liveboxandy/ZX-Spectrum-48K-Issue-2/STP/TI_TMS4532.step

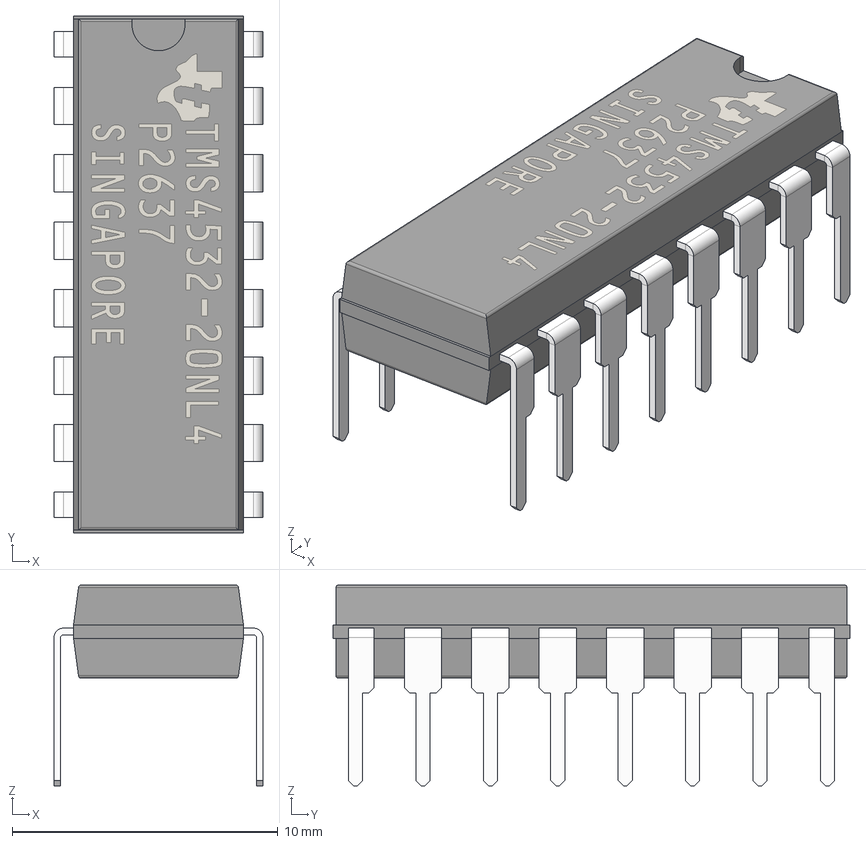
[picture p18: CAD file, 2026-09-27]
STP/TI_TMS4532.step
7.87 x 19.5 x 7.57 mm
Basic - DIP 7.62 v3
DIP Pin 14-20 v3
DIP Pin 14-20 v3(Mirror)
