liveboxandy/ZX-Spectrum-48K-Issue-2/STP/DO-41-5.10x2.60x15.24.STEP

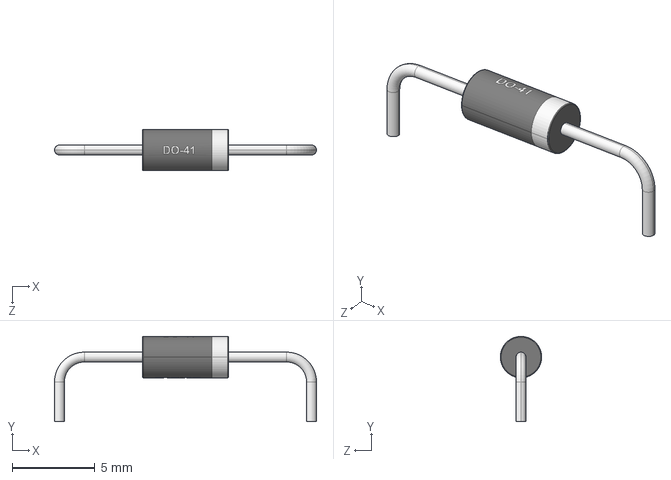
[picture p19: CAD file, 2026-09-27]
STP/DO-41-5.10x2.60x15.24.STEP
15.8 x 5.15 x 2.50 mm
