liveboxandy/ZX-Spectrum-48K-Issue-2/STP/Resistor-0414-11.5x4.5x20.32.STEP

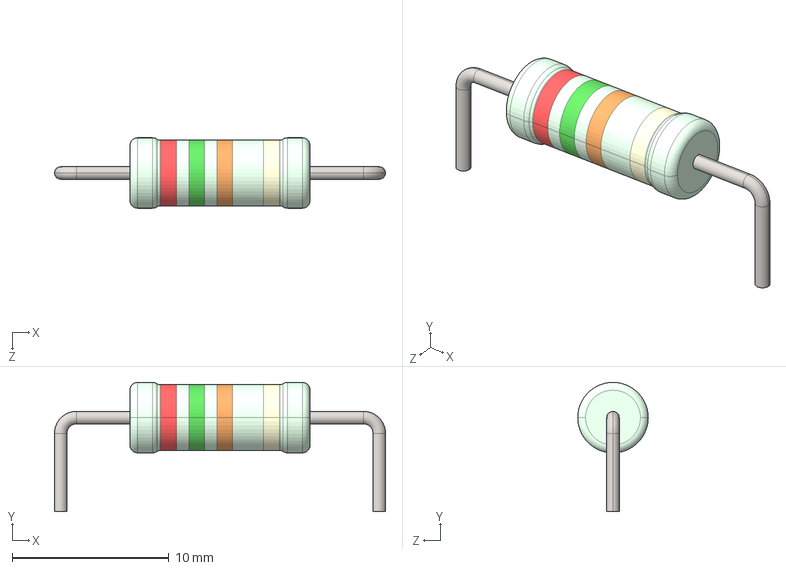
[picture p20: CAD file, 2026-09-27]
STP/Resistor-0414-11.5x4.5x20.32.STEP
21.1 x 8.25 x 4.50 mm
