liveboxandy/ZX-Spectrum-48K-Issue-2/STP/R_Axial_DIN0411_L9.9mm_D3.6mm_P12.70mm_Horizontal.step

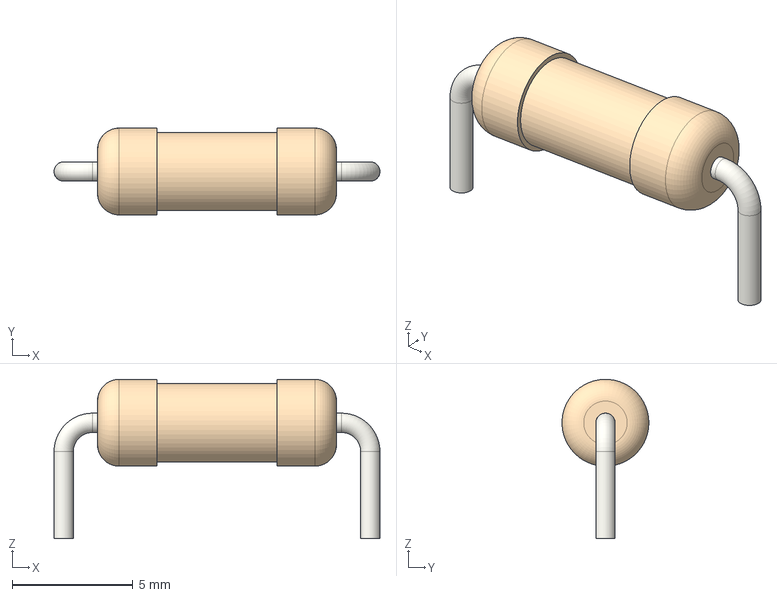
[picture p22: CAD file, 2026-09-27]
STP/R_Axial_DIN0411_L9.9mm_D3.6mm_P12.70mm_Horizontal.step
13.5 x 3.60 x 6.60 mm
