liveboxandy/ZX-Spectrum-48K-Issue-2/STP/DIP-18_W7.62mm.step

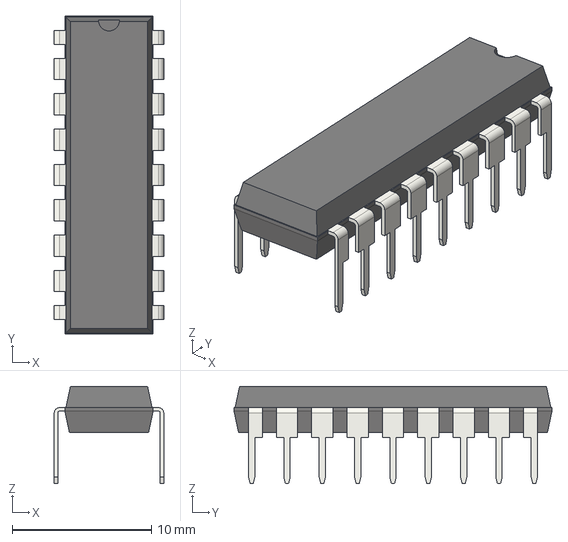
[picture p23: CAD file, 2026-09-27]
STP/DIP-18_W7.62mm.step
7.87 x 22.9 x 6.98 mm
