liveboxandy/ZX-Spectrum-48K-Issue-2/STP/Resistor-0414-11.5x4.5x15.24x3.STEP

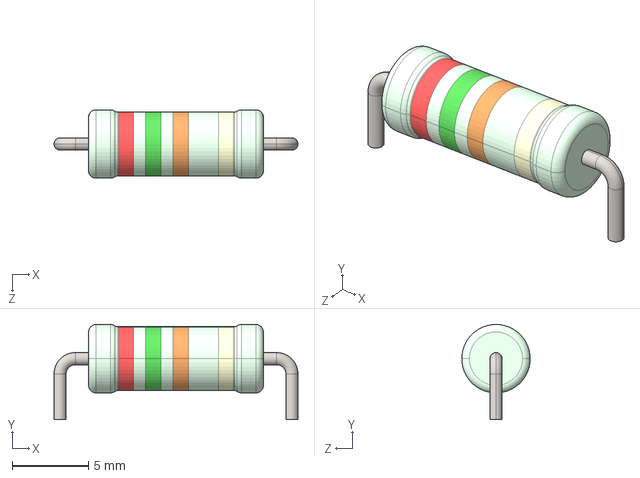
[picture p24: CAD file, 2026-09-27]
STP/Resistor-0414-11.5x4.5x15.24x3.STEP
16.0 x 6.25 x 4.50 mm
