liveboxandy/ZX-Spectrum-48K-Issue-2/STP/DO-41-5.10x2.60x10.16.STEP

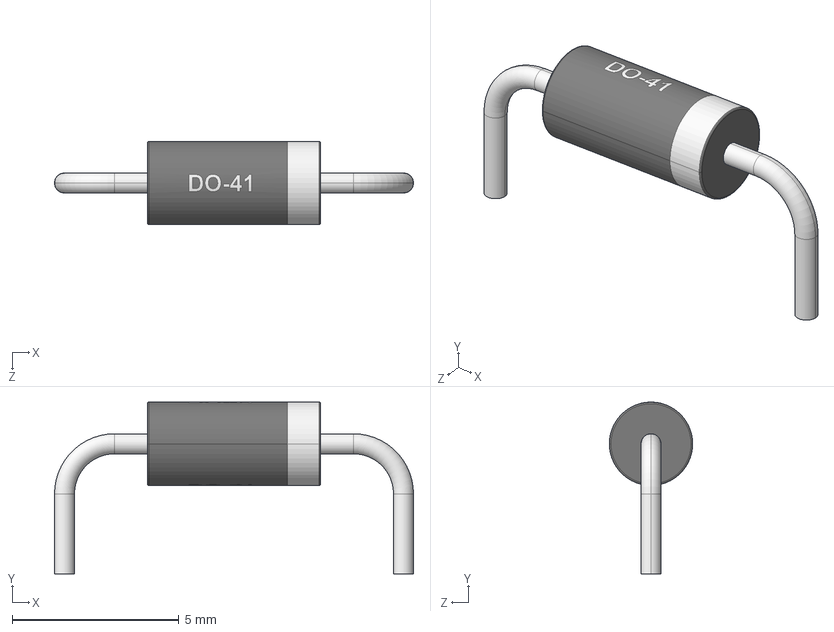
[picture p25: CAD file, 2026-09-27]
STP/DO-41-5.10x2.60x10.16.STEP
10.8 x 5.15 x 2.50 mm
