liveboxandy/ZX-Spectrum-48K-Issue-2/STP/Crystal-HC49-U.stp

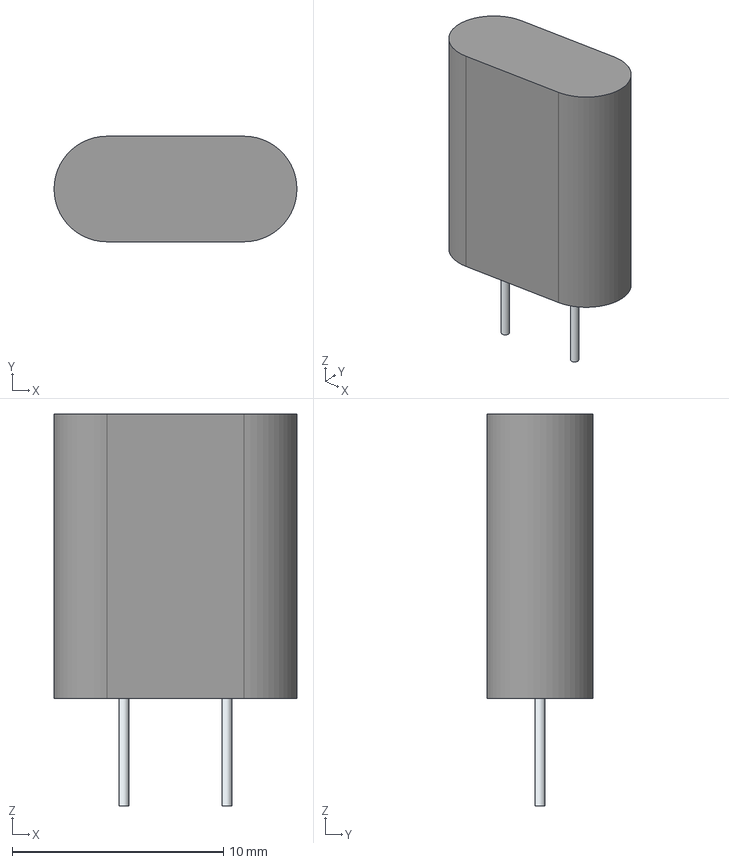
[picture p26: CAD file, 2026-09-27]
STP/Crystal-HC49-U.stp
11.5 x 5.00 x 18.6 mm
Leads
