liveboxandy/ZX-Spectrum-48K-Issue-2/STP/22-02-3053.stp

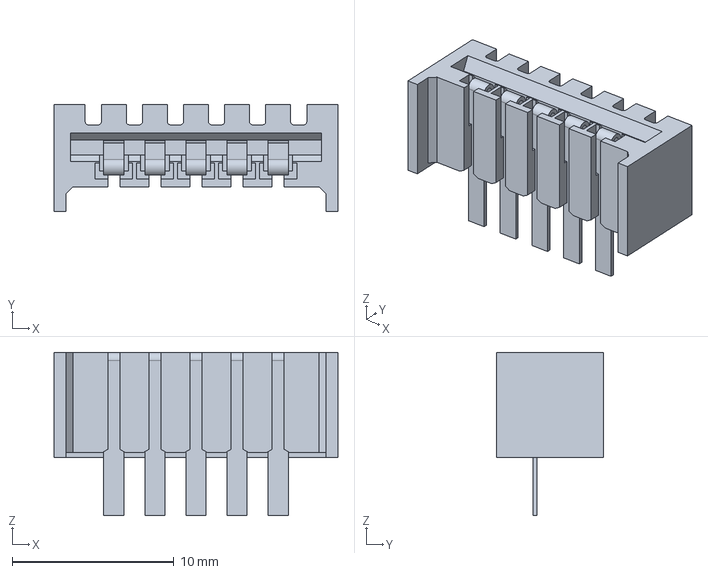
[picture p27: CAD file, 2026-09-27]
STP/22-02-3053.stp
17.6 x 6.60 x 10.1 mm
