liveboxandy/ZX-Spectrum-48K-Issue-2/STP/DIP-16_W7.62mm_Socket.step

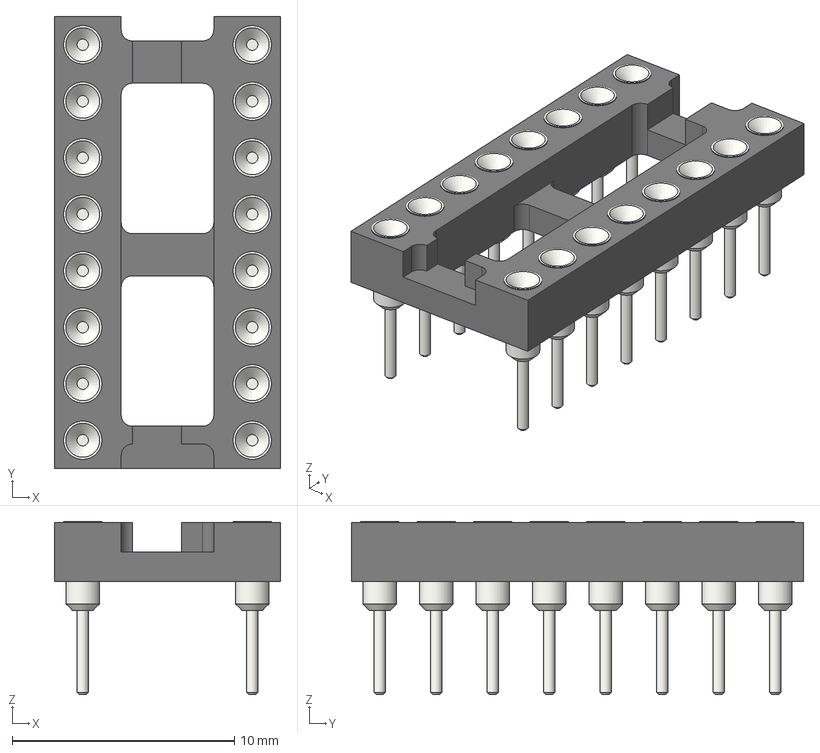
[picture p28: CAD file, 2026-09-27]
STP/DIP-16_W7.62mm_Socket.step
10.2 x 20.3 x 7.79 mm
