liveboxandy/ZX-Spectrum-48K-Issue-2/STP/DO-41-5.10x2.60x22.86.STEP

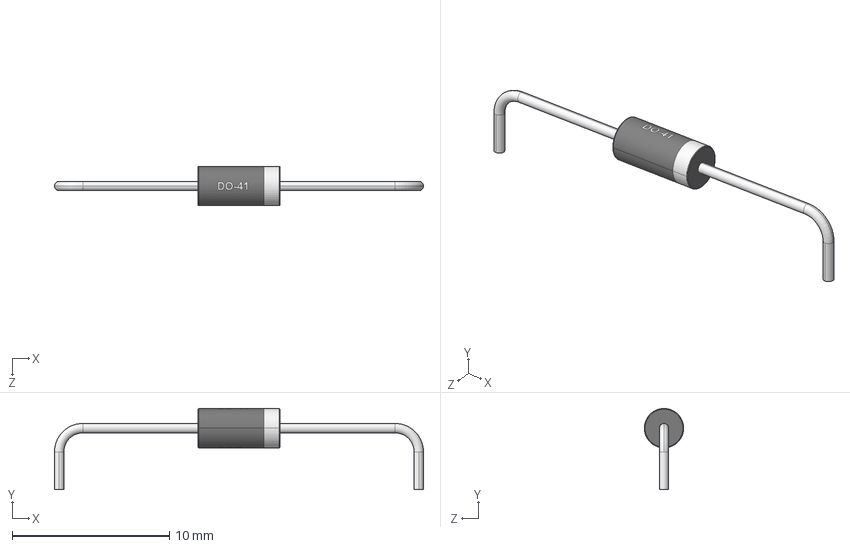
[picture p29: CAD file, 2026-09-27]
STP/DO-41-5.10x2.60x22.86.STEP
23.5 x 5.15 x 2.50 mm
