liveboxandy/ZX-Spectrum-48K-Issue-2/STP/DIP-14_W7.62mm_Socket.step

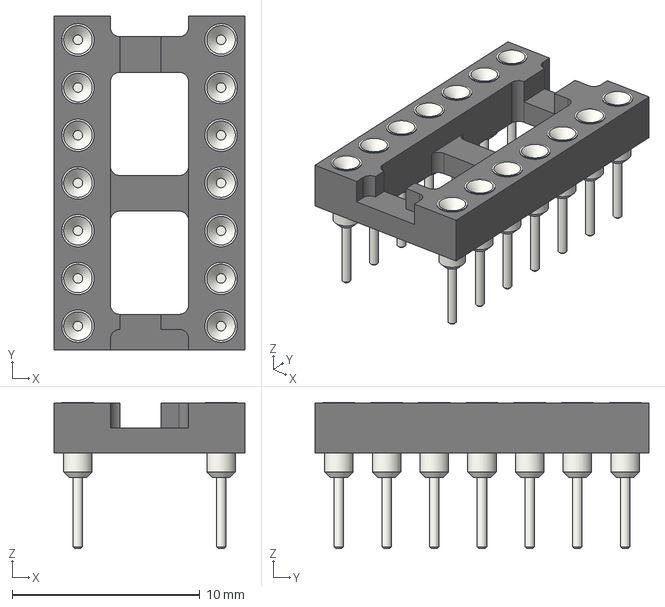
[picture p30: CAD file, 2026-09-27]
STP/DIP-14_W7.62mm_Socket.step
10.2 x 17.8 x 7.79 mm
