liveboxandy/ZX-Spectrum-48K-Issue-2/STP/Crystal-Low.stp

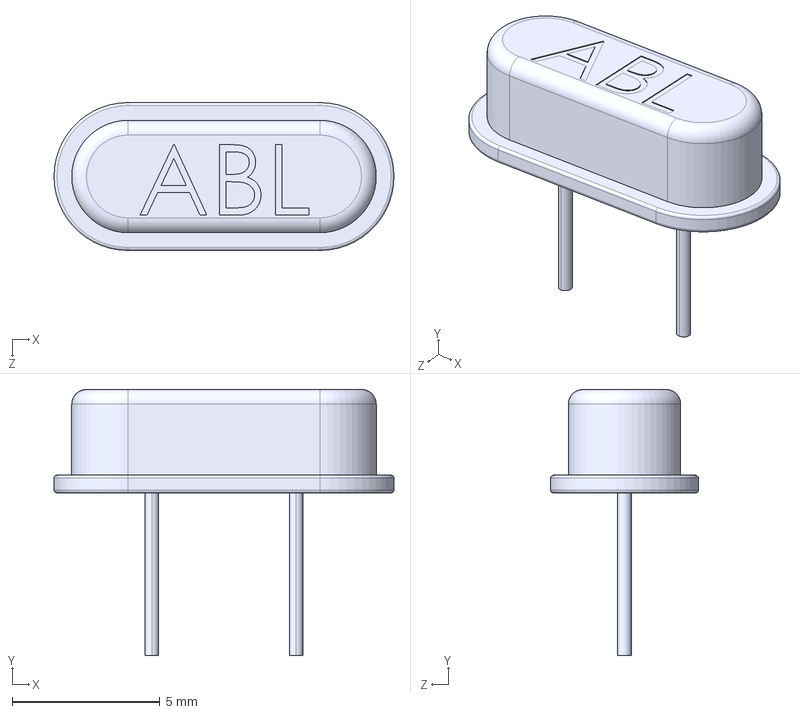
[picture p33: CAD file, 2026-09-27]
STP/Crystal-Low.stp
11.5 x 9.00 x 5.00 mm
