liveboxandy/ZX-Spectrum-48K-Issue-2/STP/Jumper.step

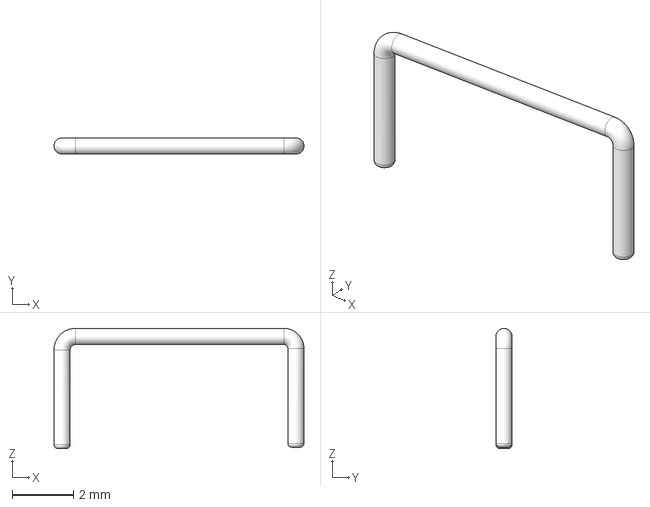
[picture p35: CAD file, 2026-09-27]
STP/Jumper.step
8.18 x 0.53 x 3.94 mm
