liveboxandy/ZX-Spectrum-48K-Issue-2/STP/LM7805CT_NOPB.stp

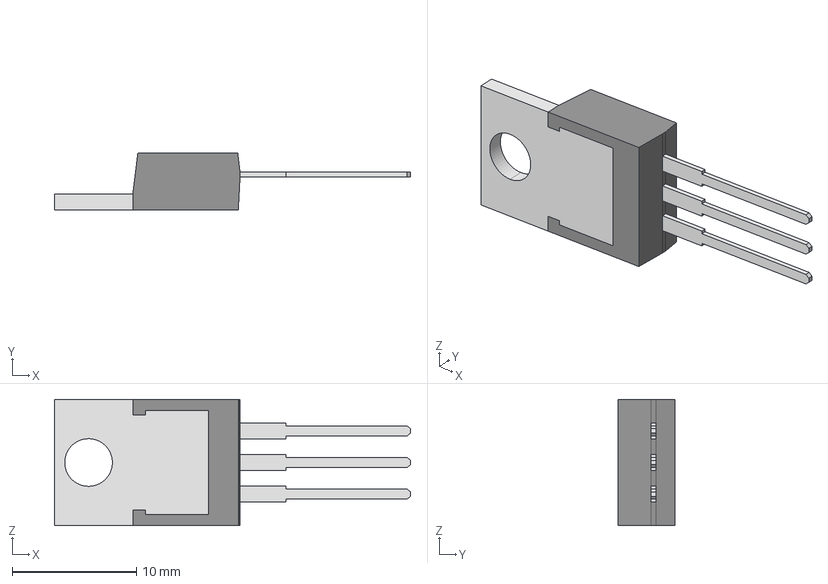
[picture p36: CAD file, 2026-09-27]
STP/LM7805CT_NOPB.stp
28.7 x 4.57 x 10.2 mm
T03B_BODY
T03B_LEAD x 3
T03B_HS
