liveboxandy/ZX-Spectrum-48K-Issue-2/STP/NS_LM1889N.step

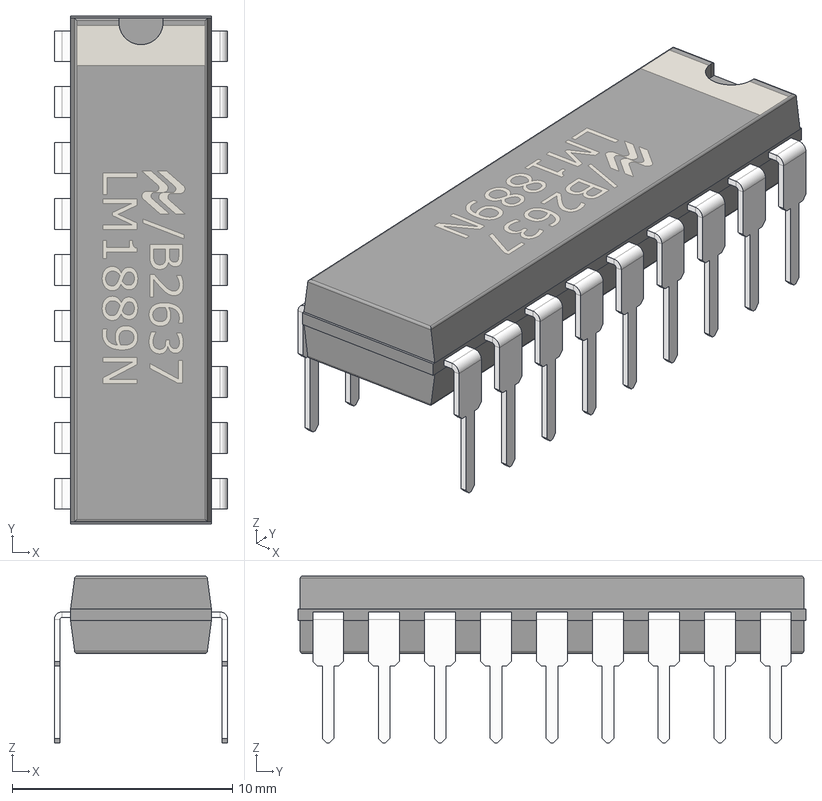
[picture p37: CAD file, 2026-09-27]
STP/NS_LM1889N.step
7.87 x 23.1 x 7.57 mm
Basic - DIP 7.62 v3
DIP Pin 14-20 v3
DIP Pin 14-20 v3(Mirror)
