liveboxandy/ZX-Spectrum-48K-Issue-2/STP/DO-35_P12.70_BA157.step

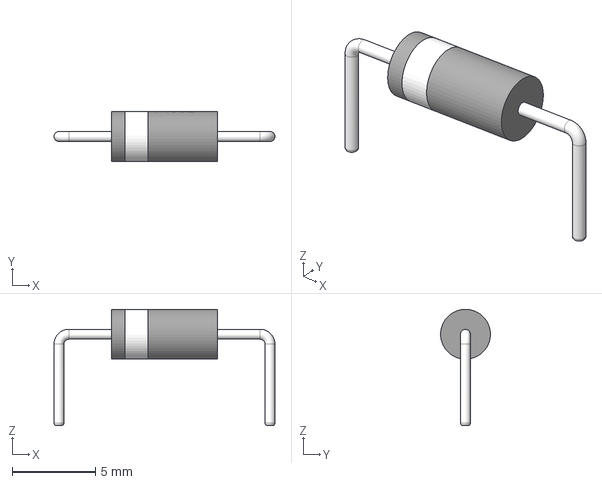
[picture p38: CAD file, 2026-09-27]
STP/DO-35_P12.70_BA157.step
13.3 x 3.00 x 7.00 mm
Wire
Diode Body
