liveboxandy/ZX-Spectrum-48K-Issue-2/STP/DIP-24_W10.16mm.step

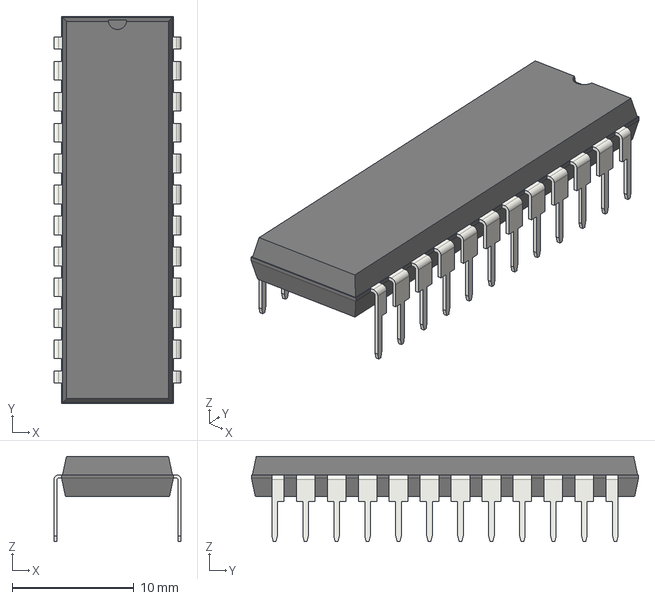
[picture p39: CAD file, 2026-09-27]
STP/DIP-24_W10.16mm.step
10.4 x 31.8 x 6.98 mm
