liveboxandy/ZX-Spectrum-48K-Issue-2/STP/LM7805 with Heatsink i3.step

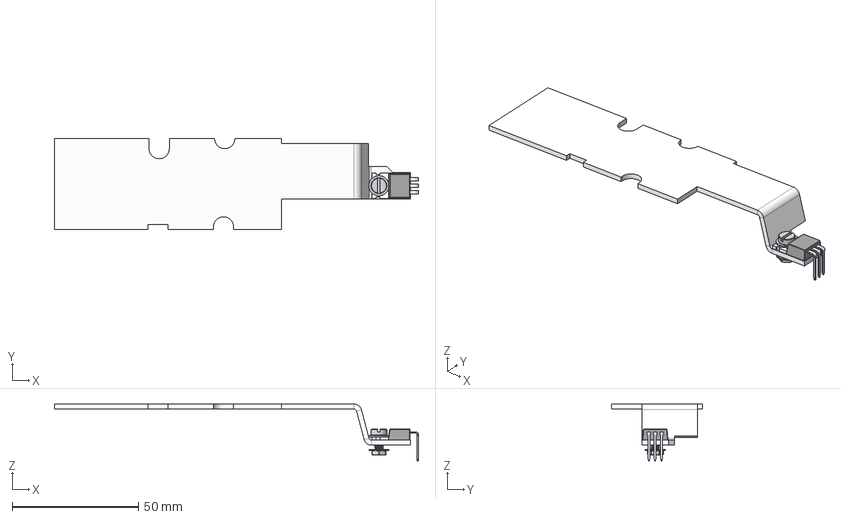
[picture p40: CAD file, 2026-09-27]
STP/LM7805 with Heatsink i3.step
144.3 x 36.0 x 22.5 mm
Heatsink
TO-220-3
Screw
93925A250_Internal Tooth Lock Washers
90695A033_Medium-Strength Steel Thin-Profile Hex Nut
Fibre Washer
