liveboxandy/ZX-Spectrum-48K-Issue-2/STP/CP 13x5x0.5x25.40.STEP

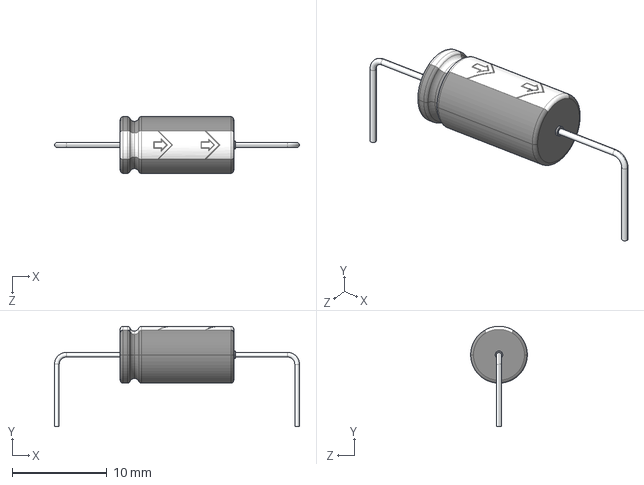
[picture p41: CAD file, 2026-09-27]
STP/CP 13x5x0.5x25.40.STEP
25.9 x 10.6 x 6.00 mm
