liveboxandy/ZX-Spectrum-48K-Issue-2/STP/Resistor-0207-6.3x2.4x15.24.STEP

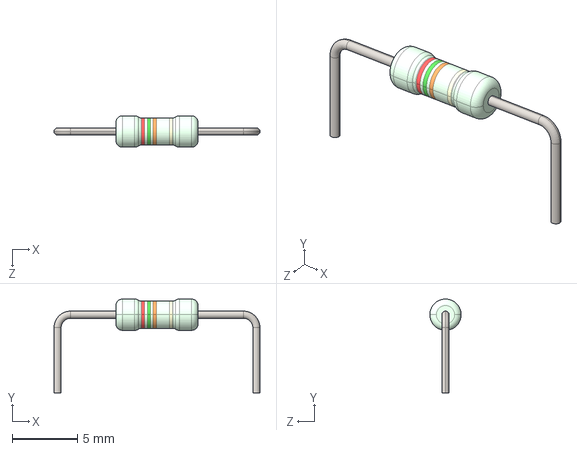
[picture p43: CAD file, 2026-09-27]
STP/Resistor-0207-6.3x2.4x15.24.STEP
15.8 x 7.20 x 2.40 mm
