liveboxandy/ZX-Spectrum-48K-Issue-2/STP/Capacitor Ceramic No Polarity axial 20.32.STEP

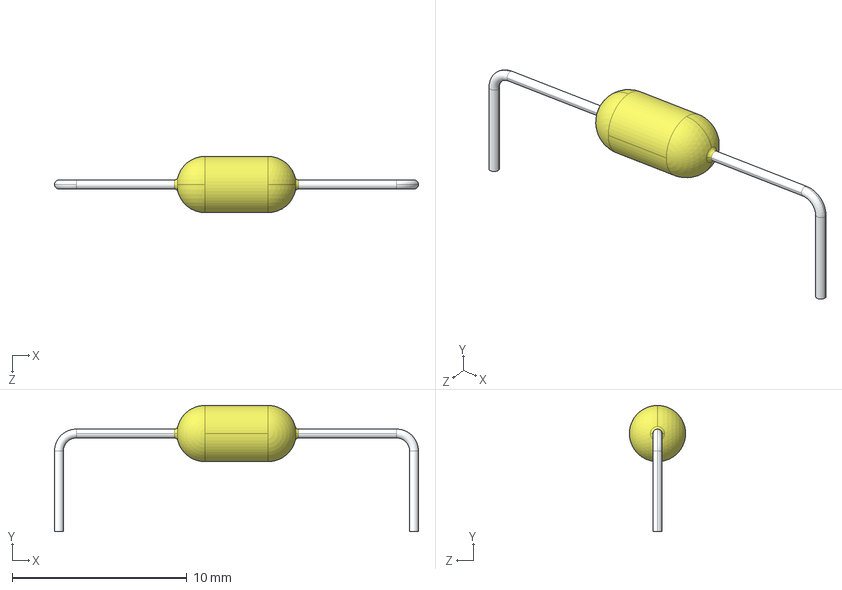
[picture p44: CAD file, 2026-09-27]
STP/Capacitor Ceramic No Polarity axial 20.32.STEP
20.8 x 7.22 x 3.22 mm
