liveboxandy/ZX-Spectrum-48K-Issue-2/STP/CP 13x5x0.5x17.78.STEP

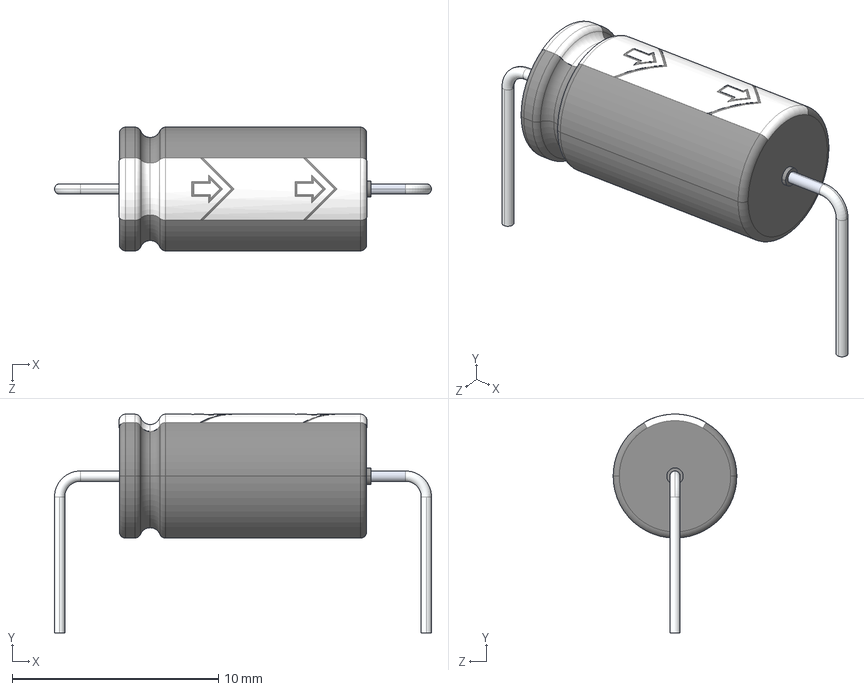
[picture p46: CAD file, 2026-09-27]
STP/CP 13x5x0.5x17.78.STEP
18.3 x 10.6 x 6.00 mm
