liveboxandy/ZX-Spectrum-48K-Issue-2/STP/DO-41-5.10x2.60x12.70.STEP

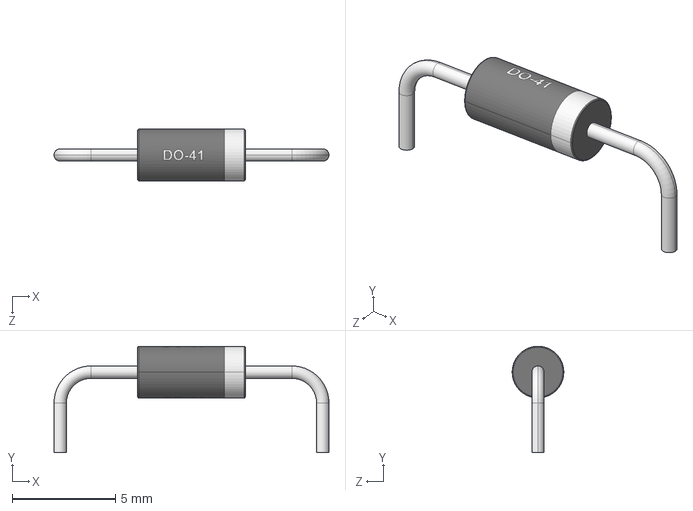
[picture p47: CAD file, 2026-09-27]
STP/DO-41-5.10x2.60x12.70.STEP
13.3 x 5.15 x 2.50 mm
