liveboxandy/ZX-Spectrum-48K-Issue-2/STP/22-02-3083.stp

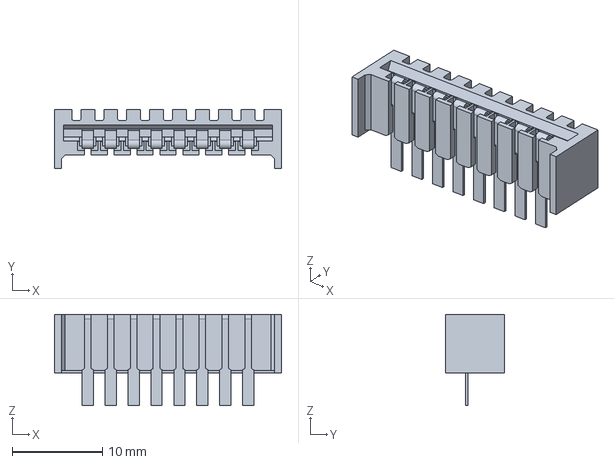
[picture p48: CAD file, 2026-09-27]
STP/22-02-3083.stp
25.2 x 6.60 x 10.1 mm
