liveboxandy/ZX-Spectrum-48K-Issue-2/STP/Pot 3339P-1-222LF.stp

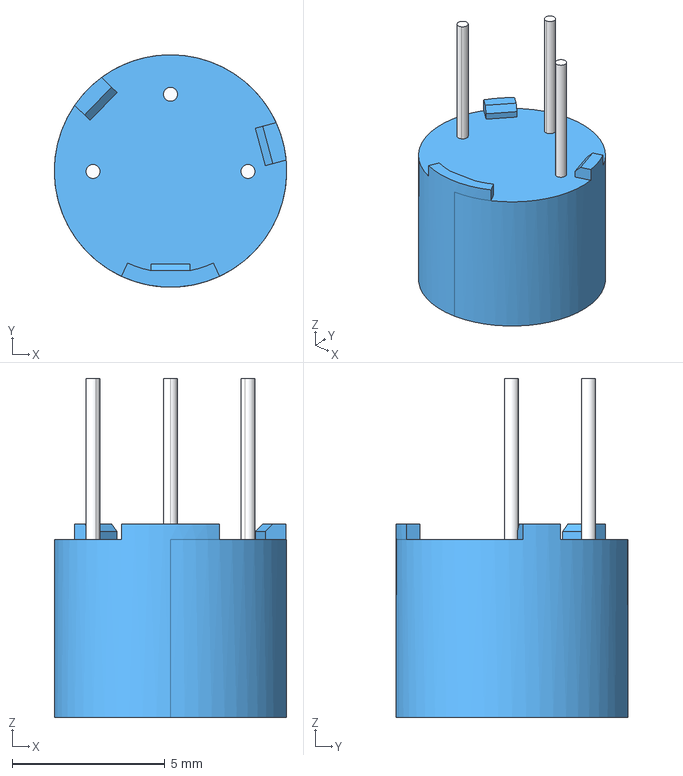
[picture p49: CAD file, 2026-09-27]
STP/Pot 3339P-1-222LF.stp
7.62 x 7.62 x 11.1 mm
