liveboxandy/ZX-Spectrum-48K-Issue-2/STP/ZTXxxx Kinked Triangle.STEP

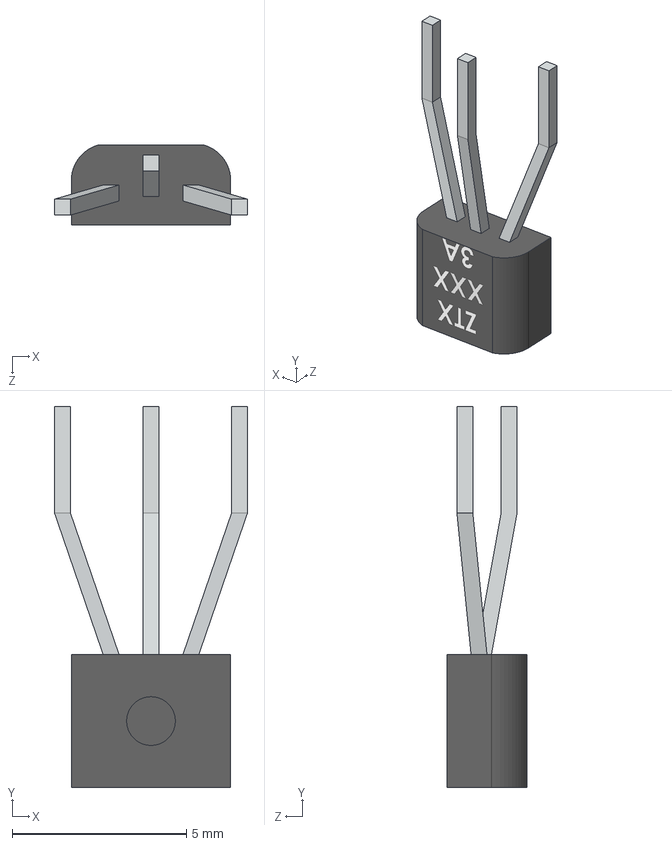
[picture p50: CAD file, 2026-09-27]
STP/ZTXxxx Kinked Triangle.STEP
5.54 x 10.9 x 2.29 mm
