liveboxandy/ZX-Spectrum-48K-Issue-2/STP/ZX Spectrum Speaker 40ohm.step

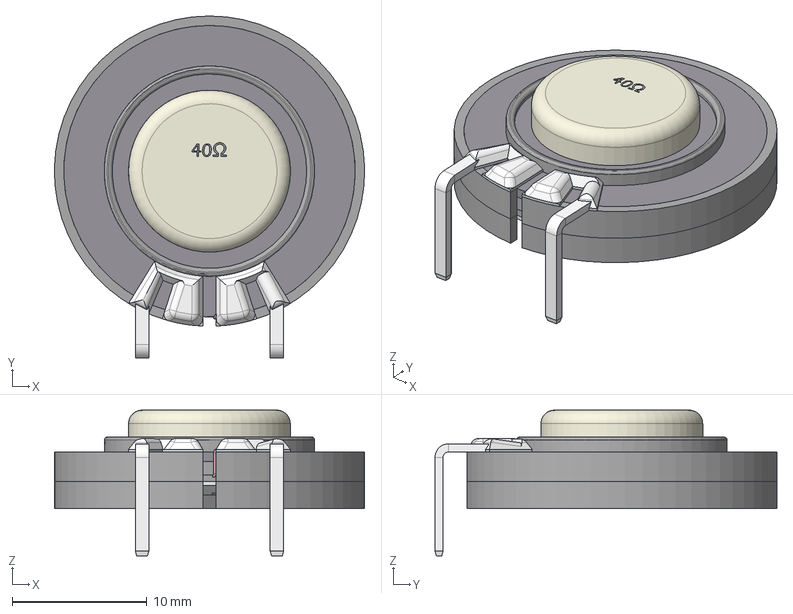
[picture p51: CAD file, 2026-09-27]
STP/ZX Spectrum Speaker 40ohm.step
23.0 x 25.4 x 10.8 mm
Magnet
Plastic Cover
Board
CopperWire
Pins
