liveboxandy/ZX-Spectrum-48K-Issue-2/STP/Resistor-0207-6.3x2.4x12.70.STEP

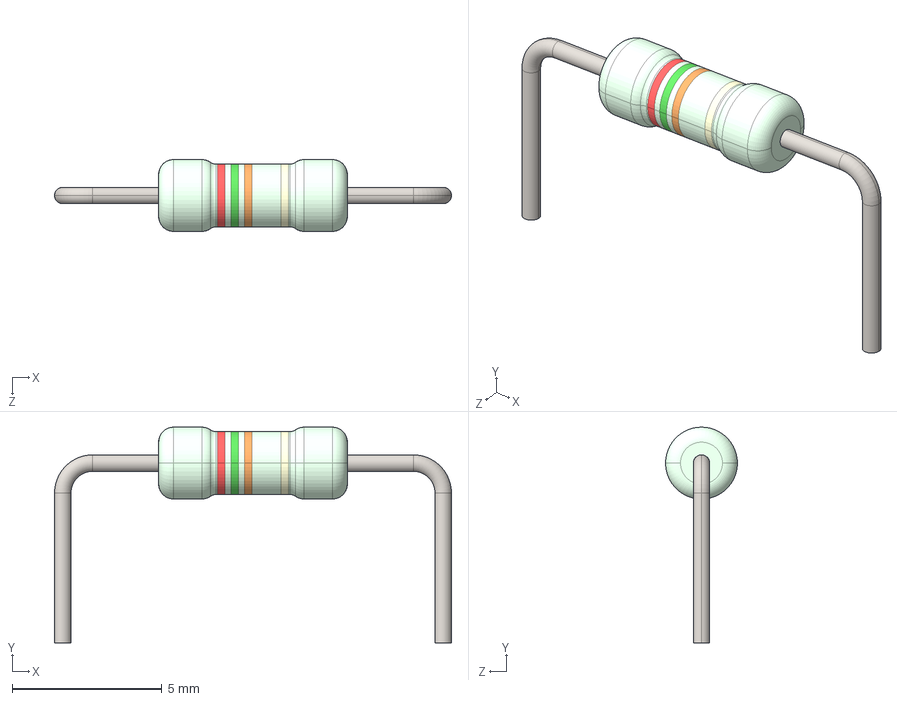
[picture p52: CAD file, 2026-09-27]
STP/Resistor-0207-6.3x2.4x12.70.STEP
13.3 x 7.20 x 2.40 mm
