liveboxandy/ZX-Spectrum-48K-Issue-2/STP/Resistor-0414-11.5x4.5x17.78.STEP

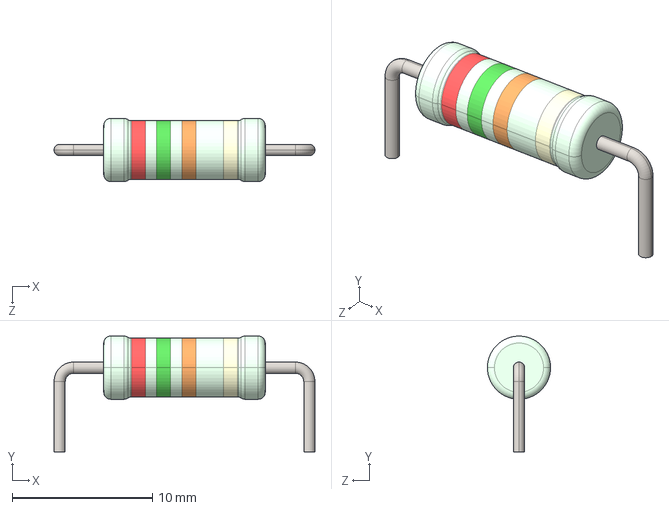
[picture p53: CAD file, 2026-09-27]
STP/Resistor-0414-11.5x4.5x17.78.STEP
18.6 x 8.25 x 4.50 mm
