liveboxandy/ZX-Spectrum-48K-Issue-2/STP/Speaker.stp

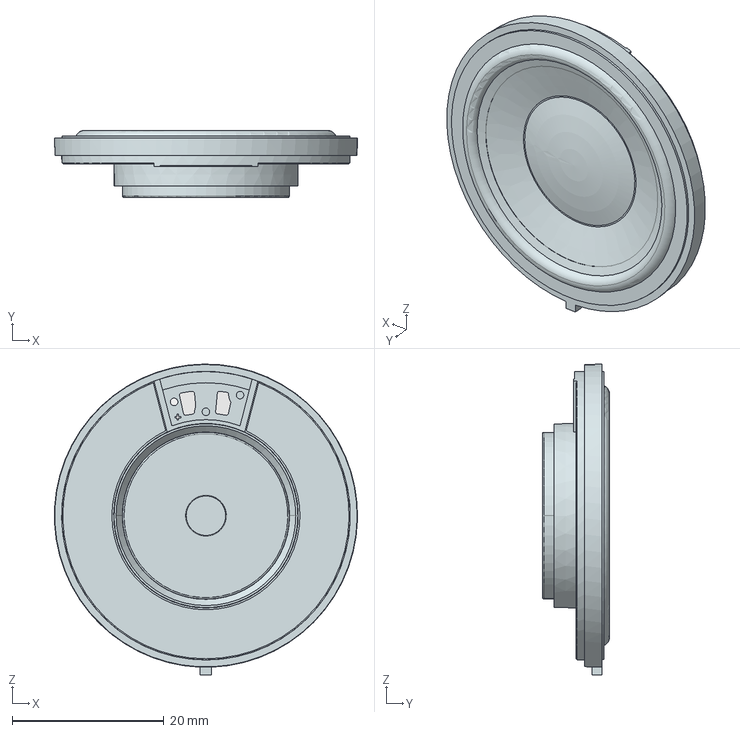
[picture p55: CAD file, 2026-09-27]
STP/Speaker.stp
40.0 x 8.88 x 41.0 mm
