liveboxandy/ZX-Spectrum-48K-Issue-2/STP/xAxial Capacitor.step

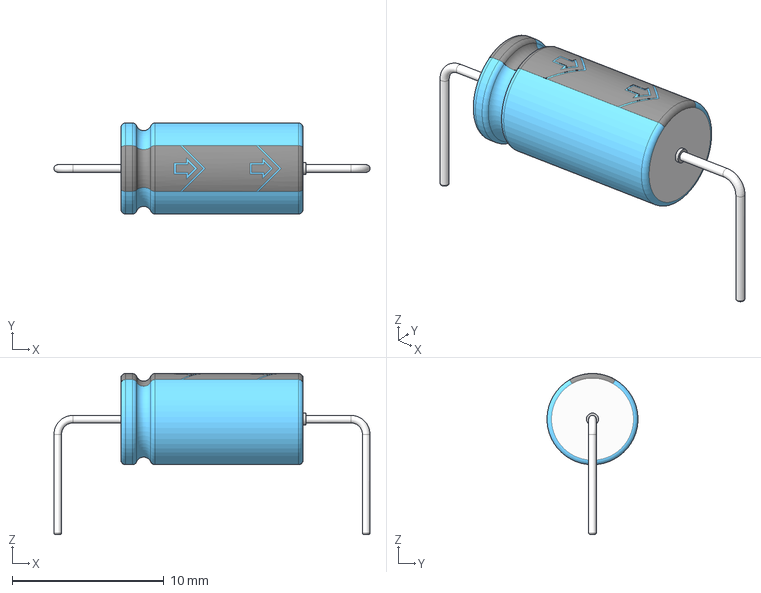
[picture p56: CAD file, 2026-09-27]
STP/xAxial Capacitor.step
20.8 x 5.99 x 10.6 mm
