liveboxandy/ZX-Spectrum-48K-Issue-2/STP/Resistor-0414-11.5x4.5x22.86.STEP

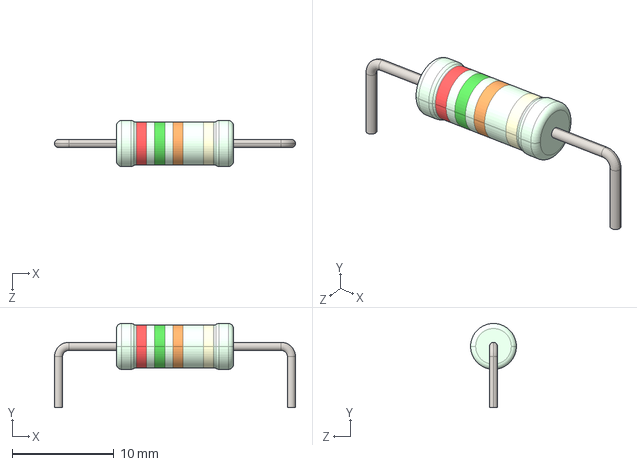
[picture p57: CAD file, 2026-09-27]
STP/Resistor-0414-11.5x4.5x22.86.STEP
23.7 x 8.25 x 4.50 mm
