liveboxandy/ZX-Spectrum-48K-Issue-2/STP/DO-41-5.10x2.60x20.32.STEP

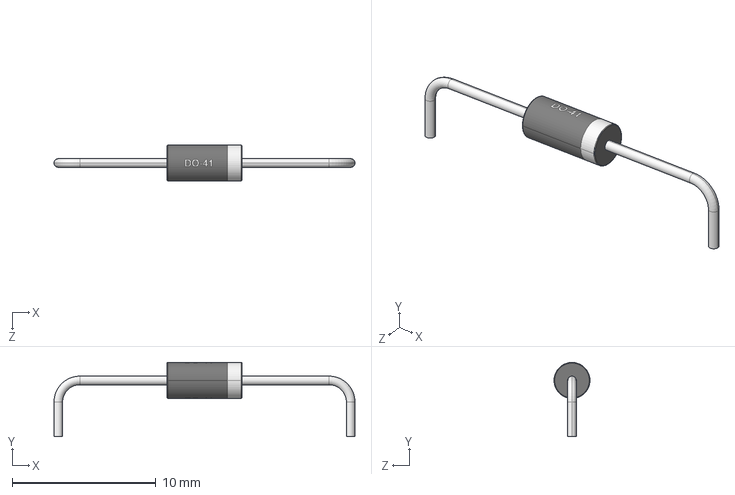
[picture p58: CAD file, 2026-09-27]
STP/DO-41-5.10x2.60x20.32.STEP
20.9 x 5.15 x 2.50 mm
