liveboxandy/ZX-Spectrum-48K-Issue-2/STP/CMS-1805-24SP.stp

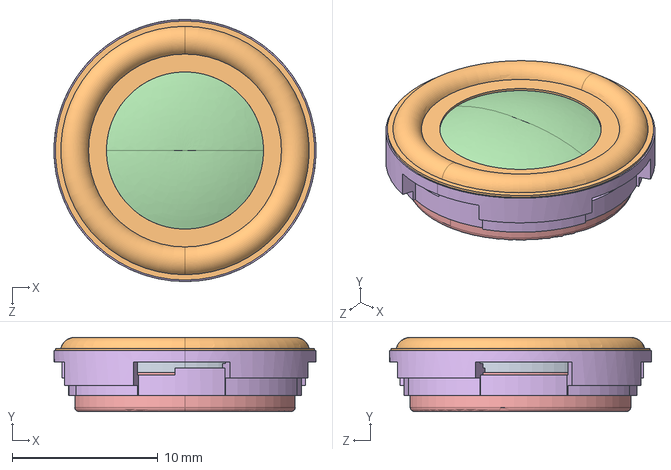
[picture p59: CAD file, 2026-09-27]
STP/CMS-1805-24SP.stp
18.0 x 5.10 x 18.0 mm
