liveboxandy/ZX-Spectrum-48K-Issue-2/STP/Capacitor Ceramic No Polarity axial 25.40.STEP

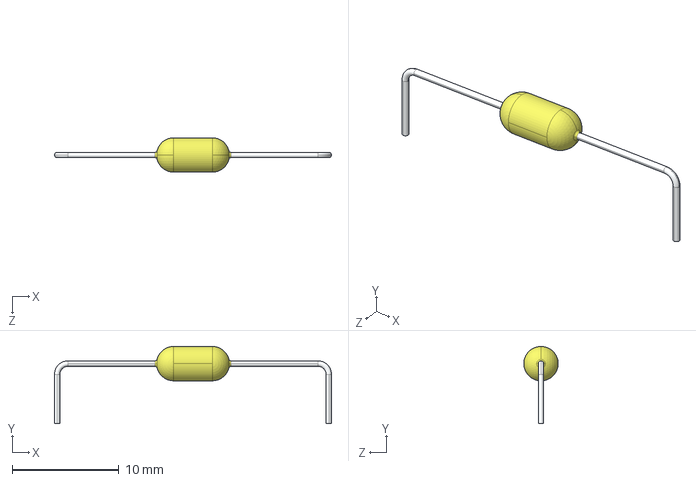
[picture p61: CAD file, 2026-09-27]
STP/Capacitor Ceramic No Polarity axial 25.40.STEP
25.9 x 7.22 x 3.22 mm
