liveboxandy/ZX-Spectrum-48K-Issue-2/STP/DO-35_3.90x1.90x0.60x17.78.STEP

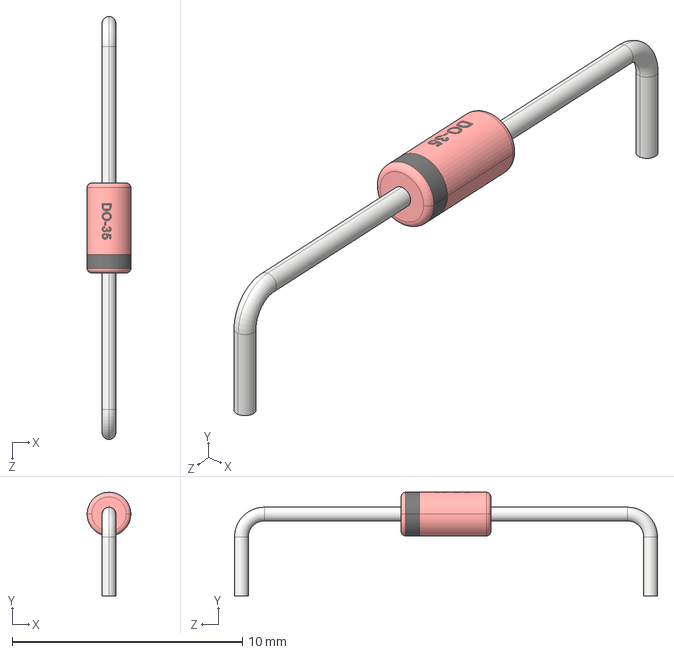
[picture p62: CAD file, 2026-09-27]
STP/DO-35_3.90x1.90x0.60x17.78.STEP
1.90 x 4.50 x 18.4 mm
