liveboxandy/ZX-Spectrum-48K-Issue-2/STP/Resistor-0207-6.3x2.4x22.86.STEP

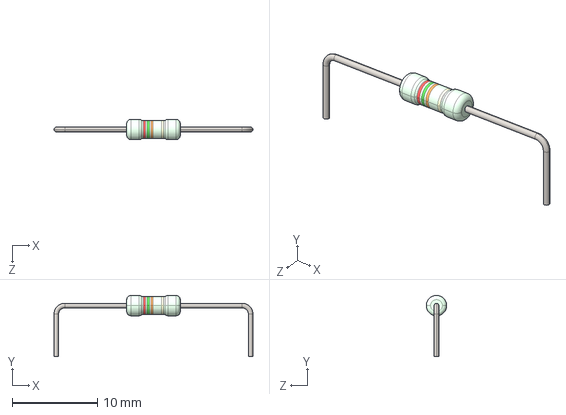
[picture p63: CAD file, 2026-09-27]
STP/Resistor-0207-6.3x2.4x22.86.STEP
23.4 x 7.20 x 2.40 mm
