liveboxandy/ZX-Spectrum-48K-Issue-2/STP/WireLink 7.62mm 1430-3.STEP

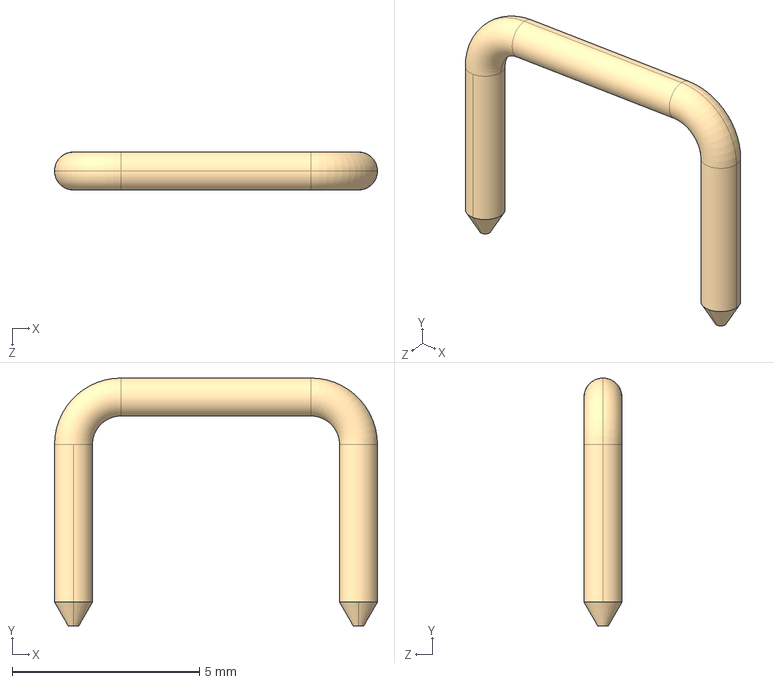
[picture p64: CAD file, 2026-09-27]
STP/WireLink 7.62mm 1430-3.STEP
8.64 x 6.63 x 1.02 mm
