liveboxandy/ZX-Spectrum-48K-Issue-2/STP/Capacitor Ceramic No Polarity axial 10.16.STEP

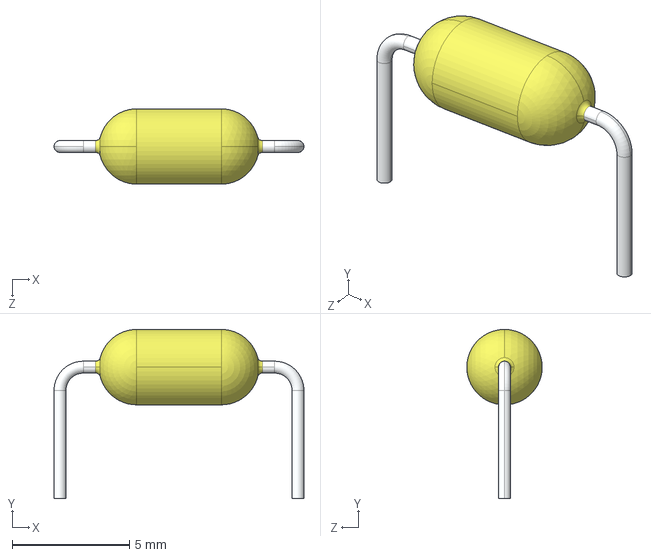
[picture p65: CAD file, 2026-09-27]
STP/Capacitor Ceramic No Polarity axial 10.16.STEP
10.7 x 7.22 x 3.22 mm
