liveboxandy/ZX-Spectrum-48K-Issue-2/STP/CP 13x5x0.5x15.24.STEP

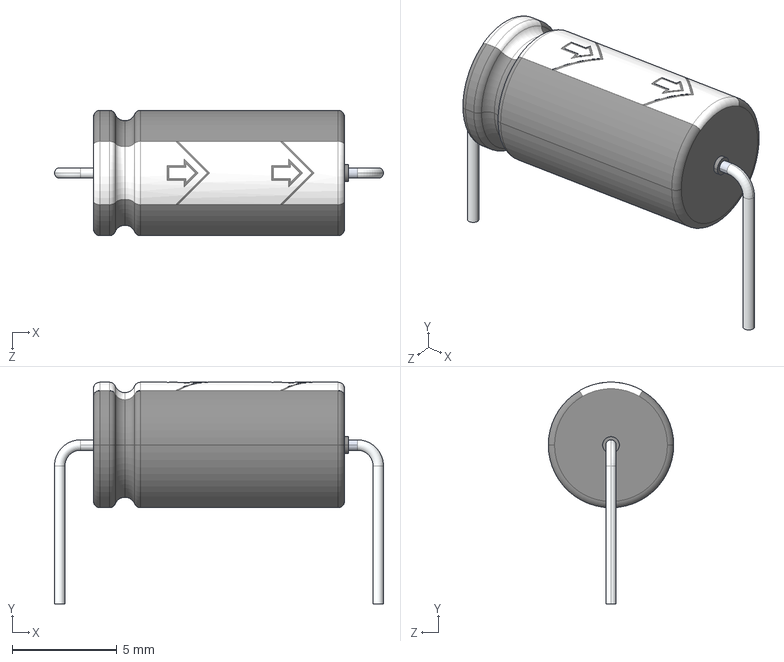
[picture p66: CAD file, 2026-09-27]
STP/CP 13x5x0.5x15.24.STEP
15.7 x 10.6 x 6.00 mm
