liveboxandy/ZX-Spectrum-48K-Issue-2/STP/5-520315-5.stp

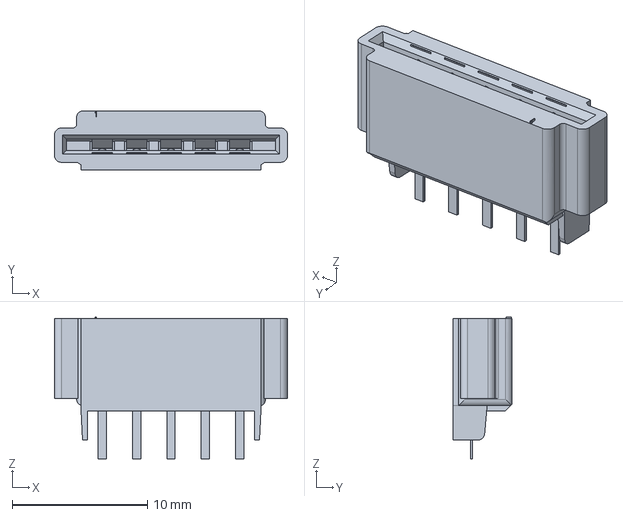
[picture p67: CAD file, 2026-09-27]
STP/5-520315-5.stp
17.2 x 4.39 x 10.5 mm
