liveboxandy/ZX-Spectrum-48K-Issue-2/STP/Transistor Kinked Lead.stp

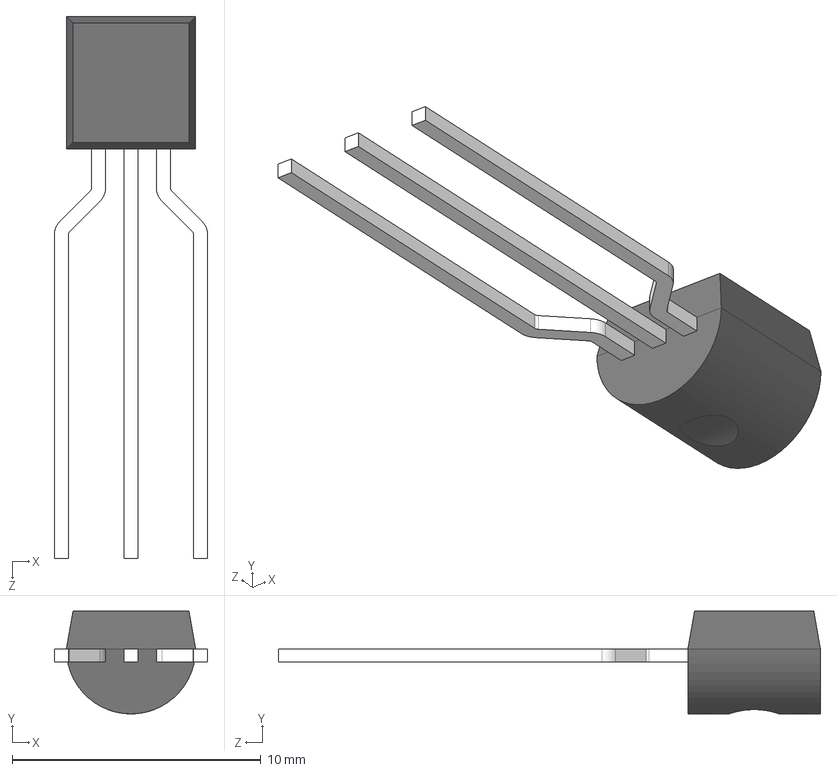
[picture p69: CAD file, 2026-09-27]
STP/Transistor Kinked Lead.stp
6.16 x 4.13 x 21.8 mm
