liveboxandy/ZX-Spectrum-48K-Issue-2/STP/Resistor-0414-11.5x4.5x25.40.STEP

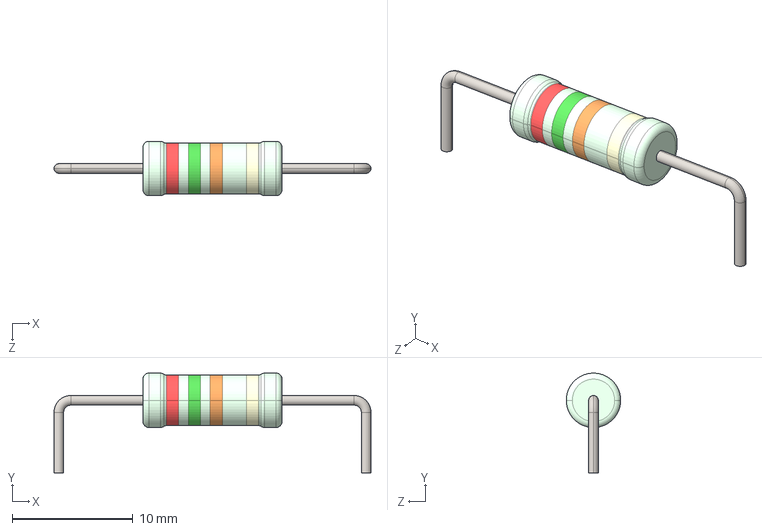
[picture p70: CAD file, 2026-09-27]
STP/Resistor-0414-11.5x4.5x25.40.STEP
26.2 x 8.25 x 4.50 mm
