liveboxandy/ZX-Spectrum-48K-Issue-2/STP/DIP-40_W15.24mm_Socket.step

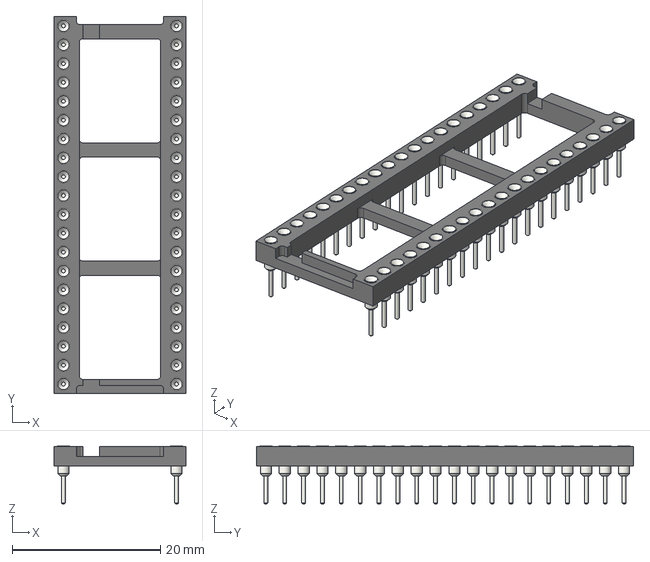
[picture p71: CAD file, 2026-09-27]
STP/DIP-40_W15.24mm_Socket.step
17.8 x 50.8 x 7.79 mm
