liveboxandy/ZX-Spectrum-48K-Issue-2/STP/DIP-24_W10.16mm_Socket.step

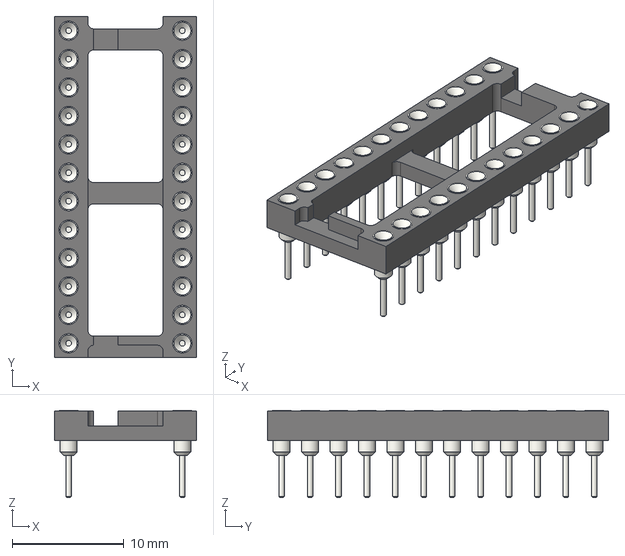
[picture p72: CAD file, 2026-09-27]
STP/DIP-24_W10.16mm_Socket.step
12.7 x 30.5 x 7.79 mm
