liveboxandy/ZX-Spectrum-48K-Issue-2/STP/CP 13x5x0.5x22.86.STEP

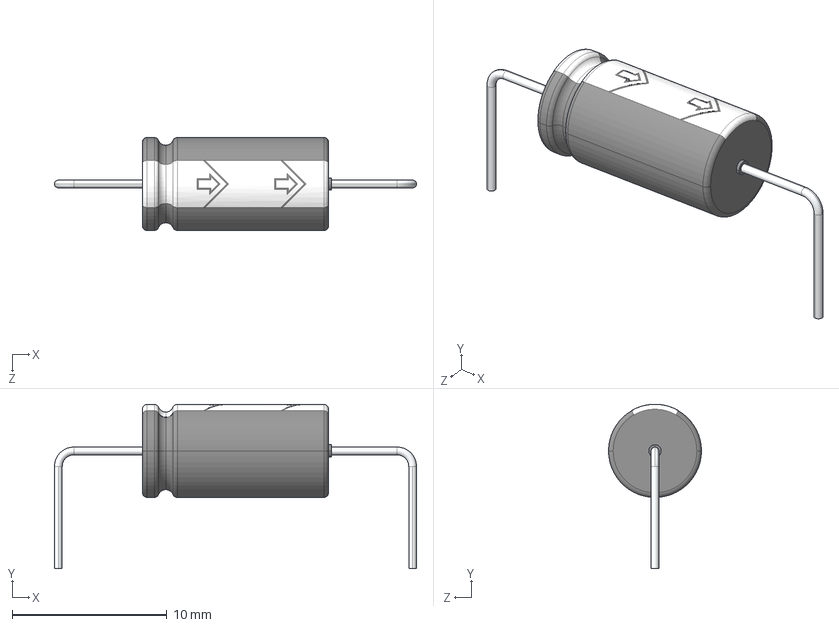
[picture p73: CAD file, 2026-09-27]
STP/CP 13x5x0.5x22.86.STEP
23.4 x 10.6 x 6.00 mm
