liveboxandy/ZX-Spectrum-48K-Issue-2/STP/Capacitor Ceramic No Polarity axial 22.86.STEP

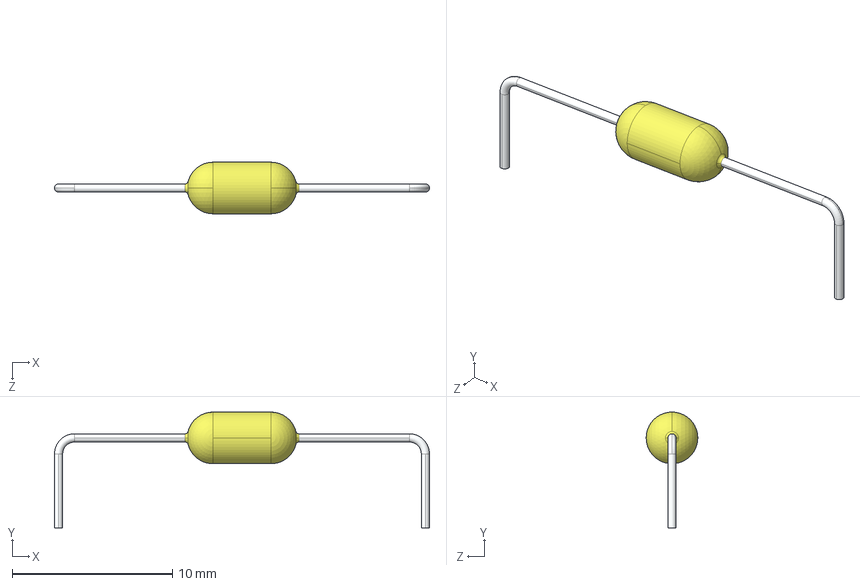
[picture p74: CAD file, 2026-09-27]
STP/Capacitor Ceramic No Polarity axial 22.86.STEP
23.4 x 7.22 x 3.22 mm
