liveboxandy/ZX-Spectrum-48K-Issue-2/STP/DC Power Connector FC68148_20DC10A_202.1mm.STP

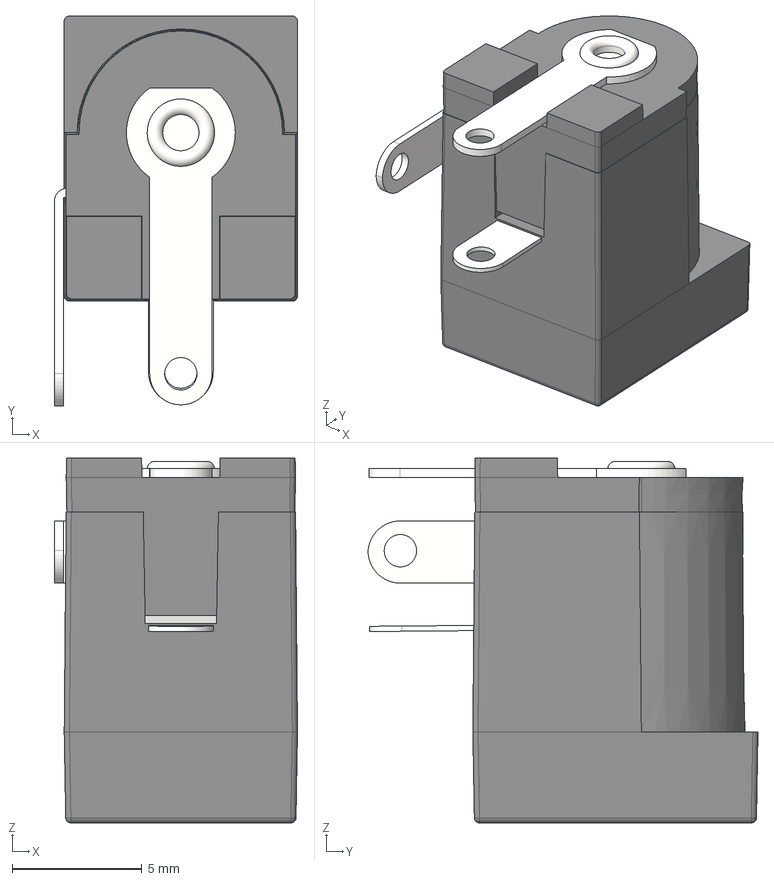
[picture p75: CAD file, 2026-09-27]
STP/DC Power Connector FC68148_20DC10A_202.1mm.STP
9.37 x 15.0 x 14.1 mm
