liveboxandy/ZX-Spectrum-48K-Issue-2/STP/DO-35_3.90x1.90x0.60x25.40.STEP

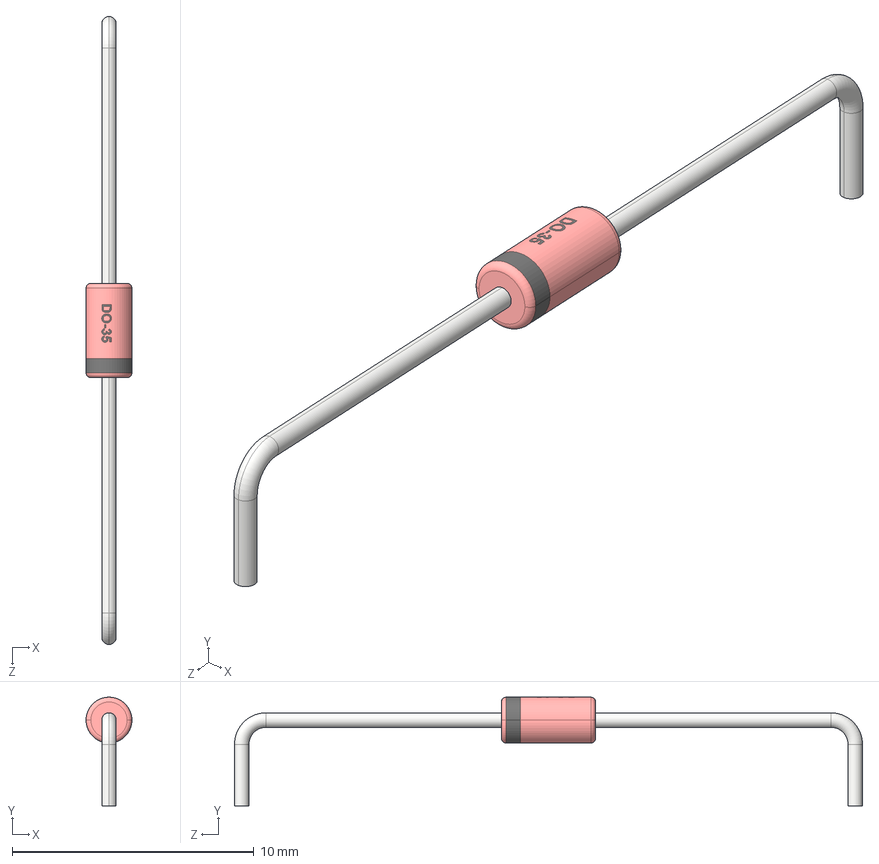
[picture p76: CAD file, 2026-09-27]
STP/DO-35_3.90x1.90x0.60x25.40.STEP
1.90 x 4.50 x 26.0 mm
