liveboxandy/ZX-Spectrum-48K-Issue-2/STP/CONN_5-520315-8_TYC.stp

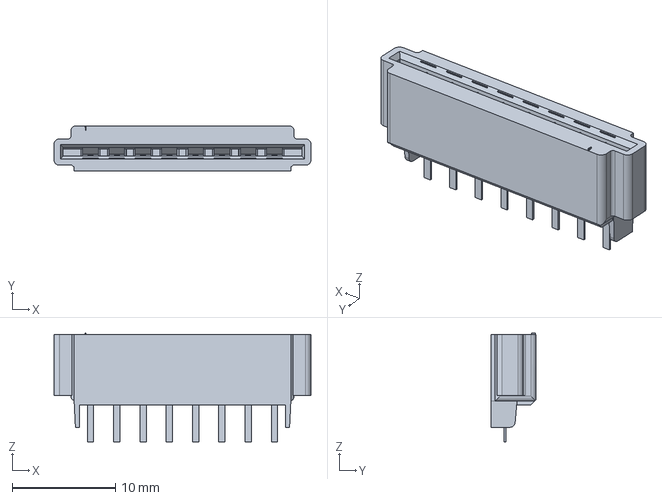
[picture p77: CAD file, 2026-09-27]
STP/CONN_5-520315-8_TYC.stp
24.8 x 4.39 x 10.5 mm
