liveboxandy/ZX-Spectrum-48K-Issue-2/STP/DIP-28_W15.24mm_Socket.step

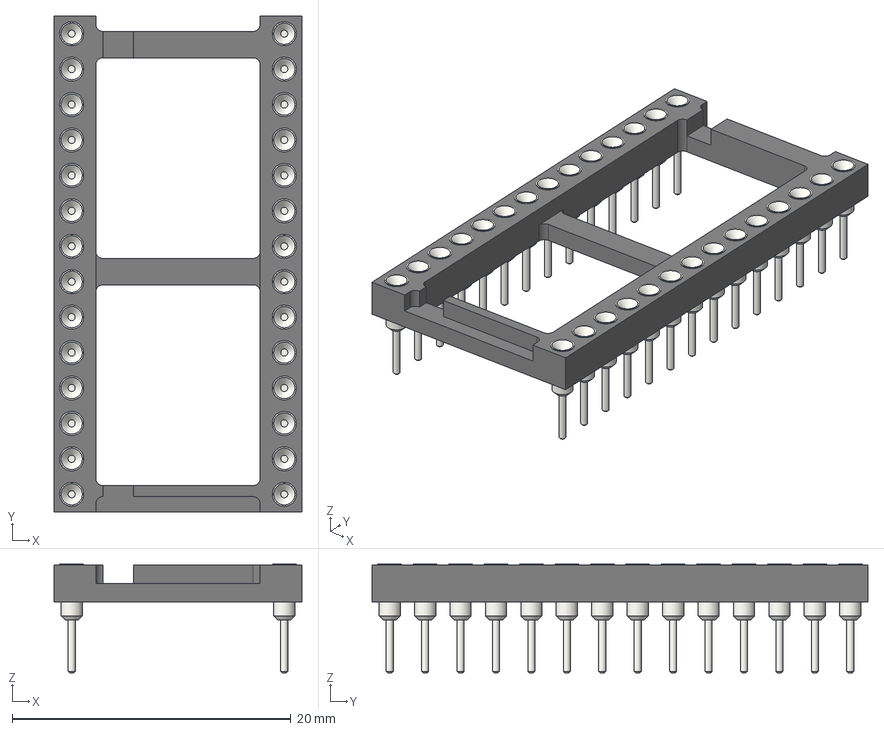
[picture p78: CAD file, 2026-09-27]
STP/DIP-28_W15.24mm_Socket.step
17.8 x 35.6 x 7.79 mm
