liveboxandy/ZX-Spectrum-48K-Issue-2/STP/DIP-28_W15.24mm.step

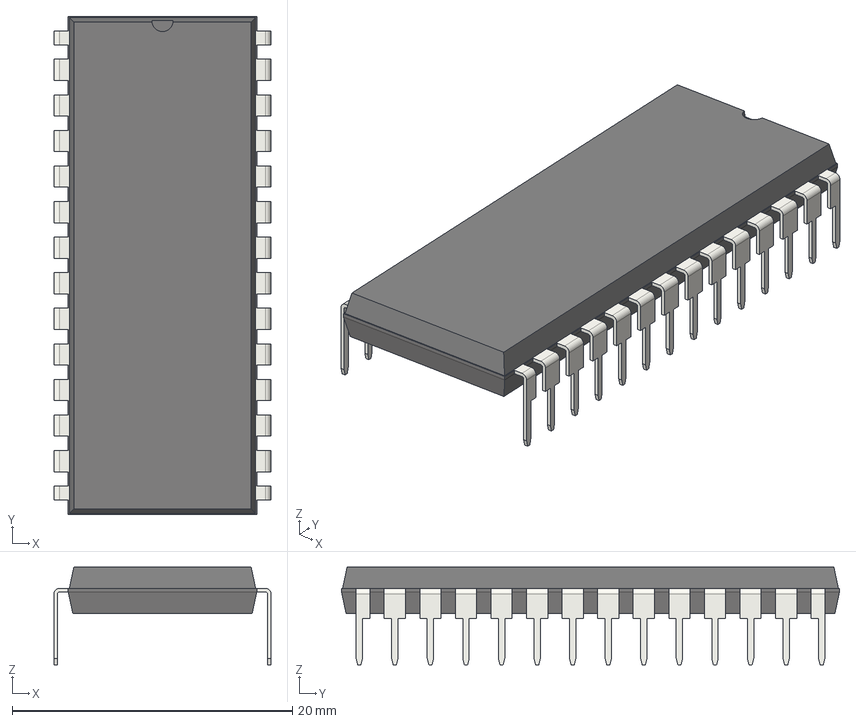
[picture p80: CAD file, 2026-09-27]
STP/DIP-28_W15.24mm.step
15.5 x 35.6 x 6.98 mm
