liveboxandy/ZX-Spectrum-48K-Issue-2/STP/TO220 Horizontal - Bent Leads.STEP

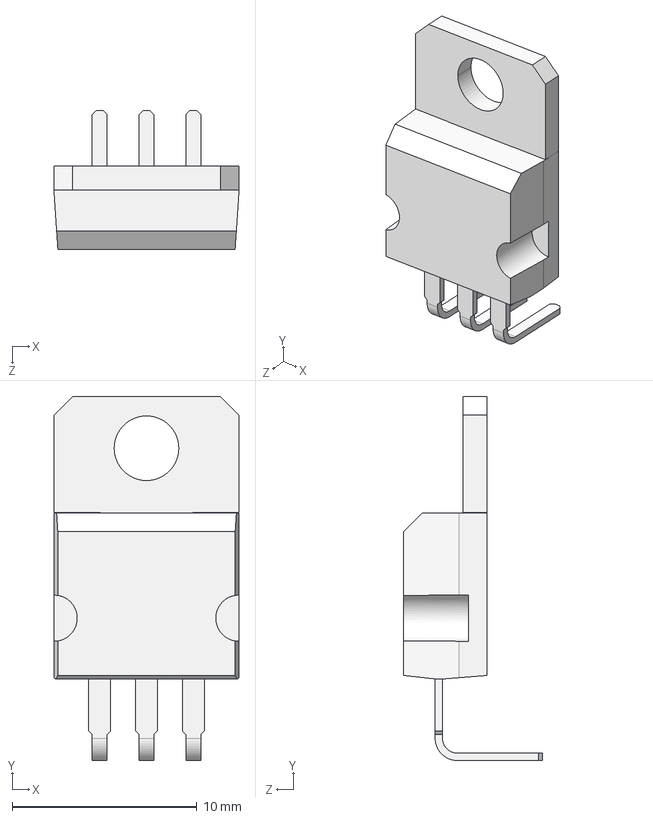
[picture p81: CAD file, 2026-09-27]
STP/TO220 Horizontal - Bent Leads.STEP
10.0 x 19.7 x 7.50 mm
