liveboxandy/ZX-Spectrum-48K-Issue-2/STP/FCR1281 S6A 6mm.stp

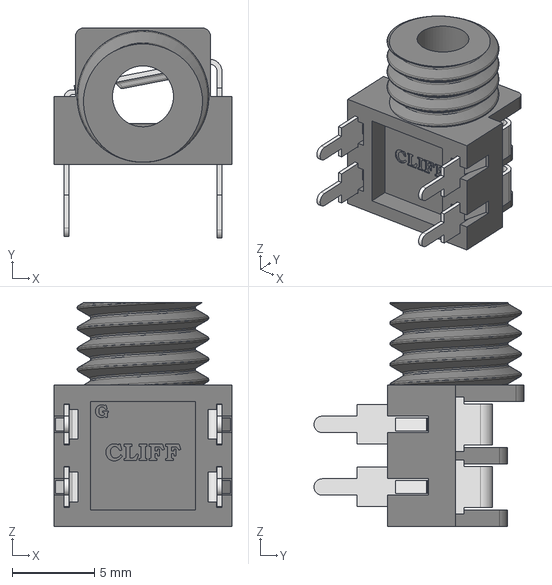
[picture p82: CAD file, 2026-09-27]
STP/FCR1281 S6A 6mm.stp
10.8 x 12.8 x 13.6 mm
