liveboxandy/ZX-Spectrum-48K-Issue-2/STP/UM1233.step

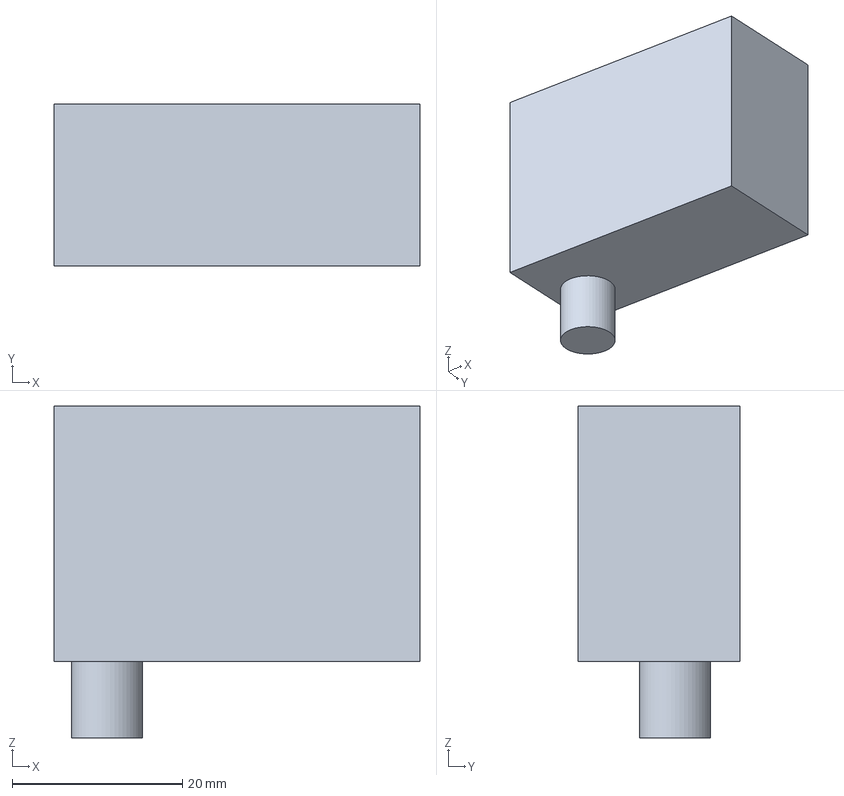
[picture p83: CAD file, 2026-09-27]
STP/UM1233.step
43.0 x 19.0 x 39.0 mm
