liveboxandy/ZX-Spectrum-48K-Issue-2/STP/Speaker SM230332-2.stp

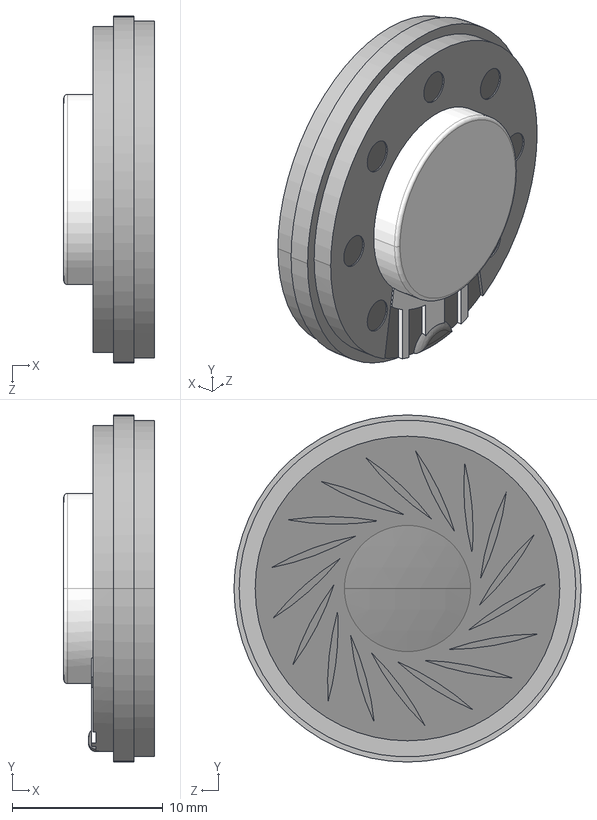
[picture p84: CAD file, 2026-09-27]
STP/Speaker SM230332-2.stp
6.00 x 23.0 x 23.0 mm
