liveboxandy/ZX-Spectrum-48K-Issue-2/STP/AUDIO_JACK_3PIN.step

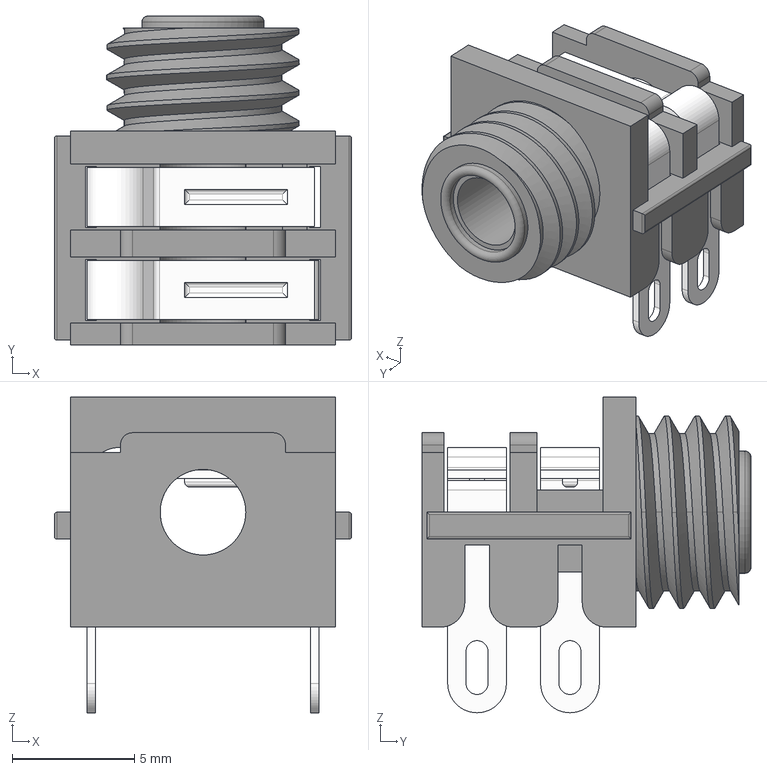
[picture p85: CAD file, 2026-09-27]
STP/AUDIO_JACK_3PIN.step
12.2 x 13.4 x 12.9 mm
Pins
Plastic Body
