liveboxandy/ZX-Spectrum-48K-Issue-2/STP/DO-41-5.10x2.60x25.40.STEP

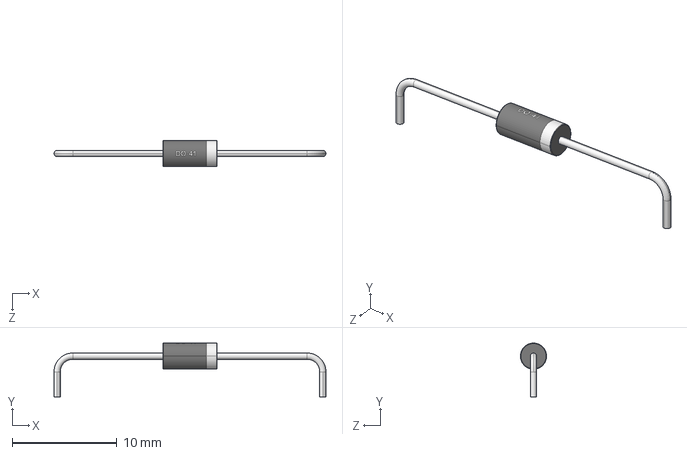
[picture p86: CAD file, 2026-09-27]
STP/DO-41-5.10x2.60x25.40.STEP
26.0 x 5.15 x 2.50 mm
