liveboxandy/ZX-Spectrum-48K-Issue-2/STP/DO-41-5.10x2.60x17.78.STEP

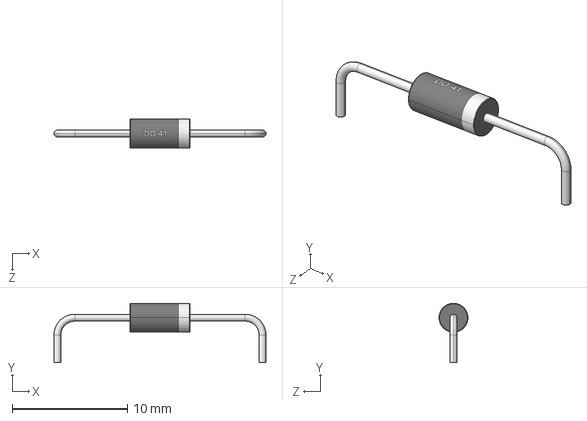
[picture p87: CAD file, 2026-09-27]
STP/DO-41-5.10x2.60x17.78.STEP
18.4 x 5.15 x 2.50 mm
