liveboxandy/ZX-Spectrum-48K-Issue-2/STP/DIP-14_W7.62mm.step

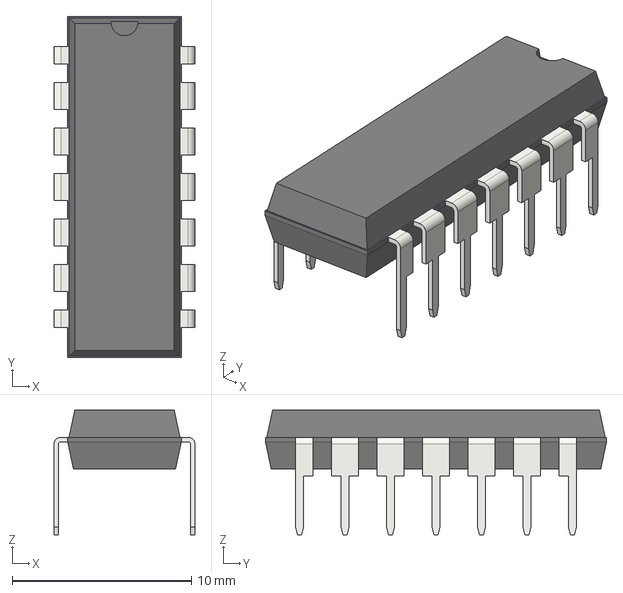
[picture p89: CAD file, 2026-09-27]
STP/DIP-14_W7.62mm.step
7.87 x 19.1 x 6.98 mm
