liveboxandy/ZX-Spectrum-48K-Issue-2/STP/CP 13x5x0.5x12.70.STEP

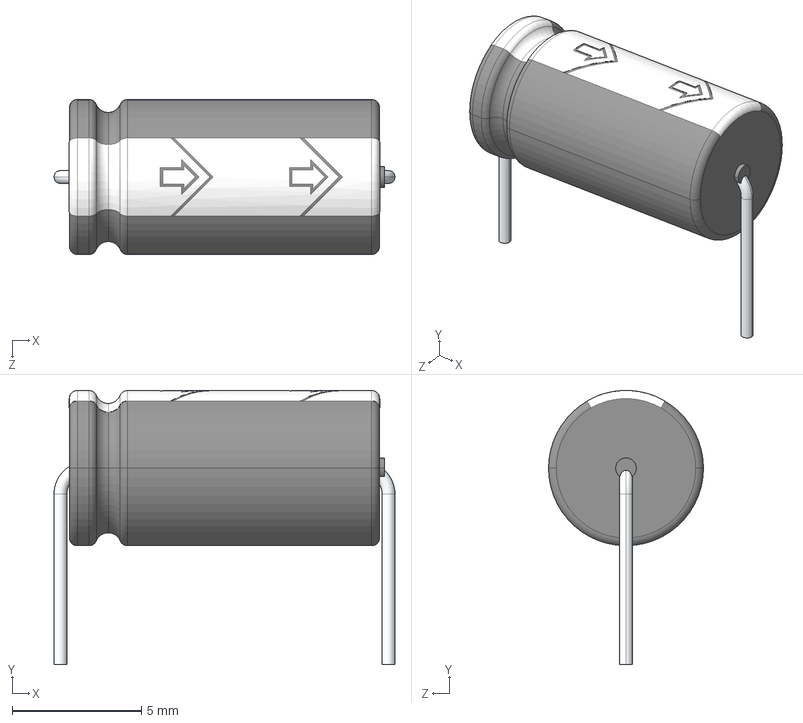
[picture p90: CAD file, 2026-09-27]
STP/CP 13x5x0.5x12.70.STEP
13.2 x 10.6 x 6.00 mm
