liveboxandy/ZX-Spectrum-48K-Issue-2/STP/Crystal-HC18-U RA.STEP

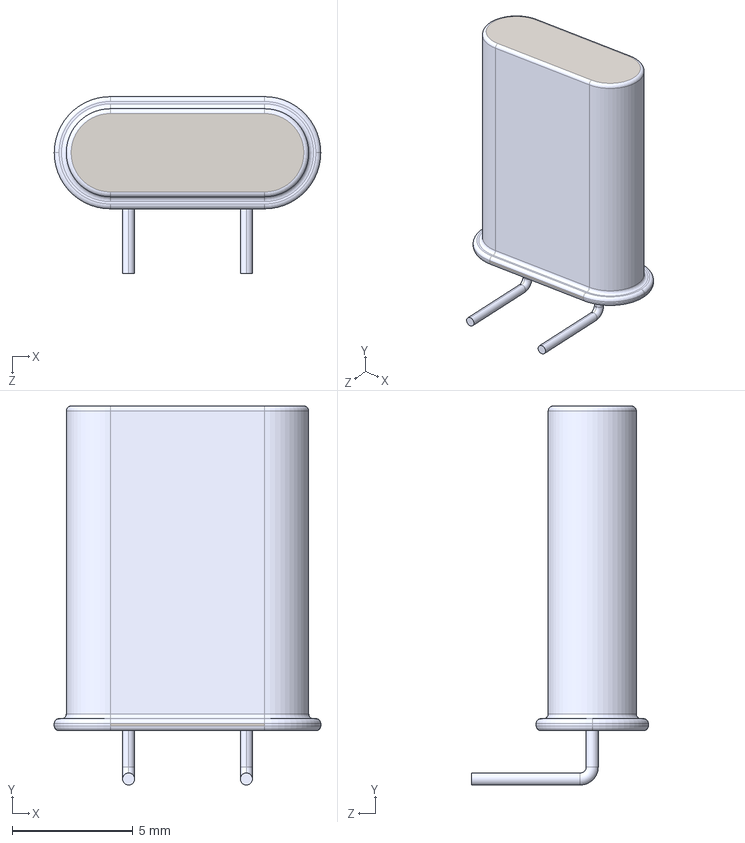
[picture p91: CAD file, 2026-09-27]
STP/Crystal-HC18-U RA.STEP
11.1 x 15.7 x 7.32 mm
