liveboxandy/ZX-Spectrum-48K-Issue-2/STP/ZX Spectrum 48k Speaker.step

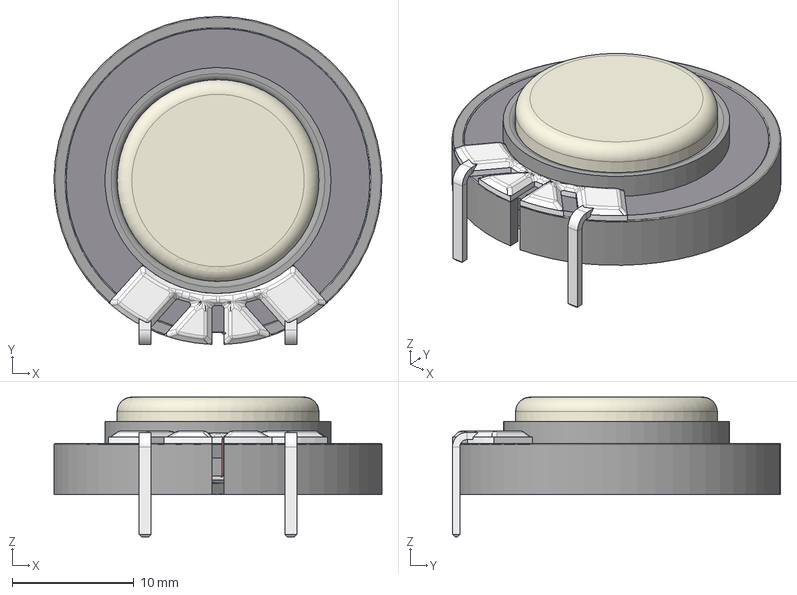
[picture p92: CAD file, 2026-09-27]
STP/ZX Spectrum 48k Speaker.step
27.0 x 27.0 x 11.5 mm
Magnet
Soldering
pins
Plastic Film
Copper Wire
