liveboxandy/ZX-Spectrum-48K-Issue-2/STP/CONN-TH_8P-P2.54_520315-8.step

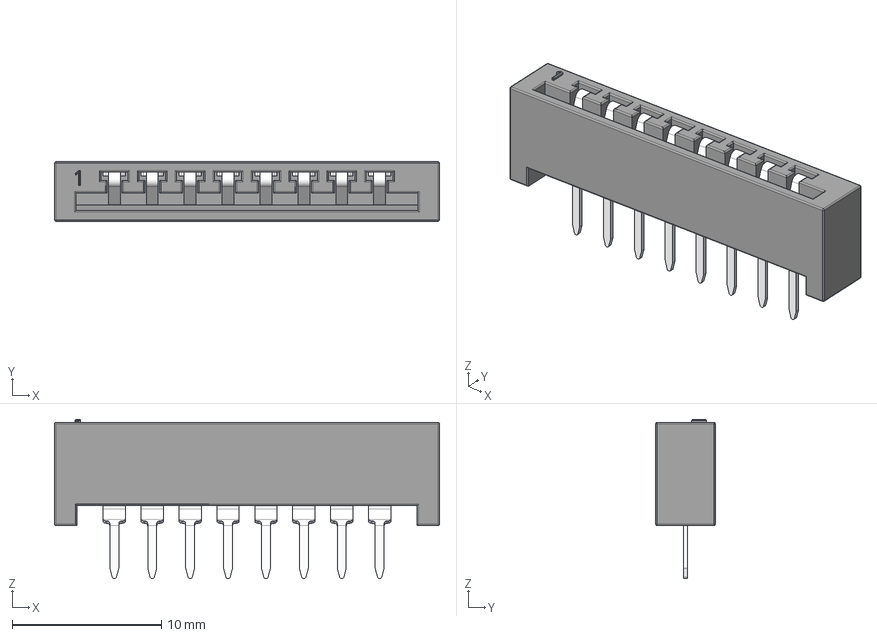
[picture p93: CAD file, 2026-09-27]
STP/CONN-TH_8P-P2.54_520315-8.step
25.8 x 4.00 x 10.7 mm
Pins
Connector Body
