liveboxandy/ZX-Spectrum-48K-Issue-2/STP/PJ-322.step

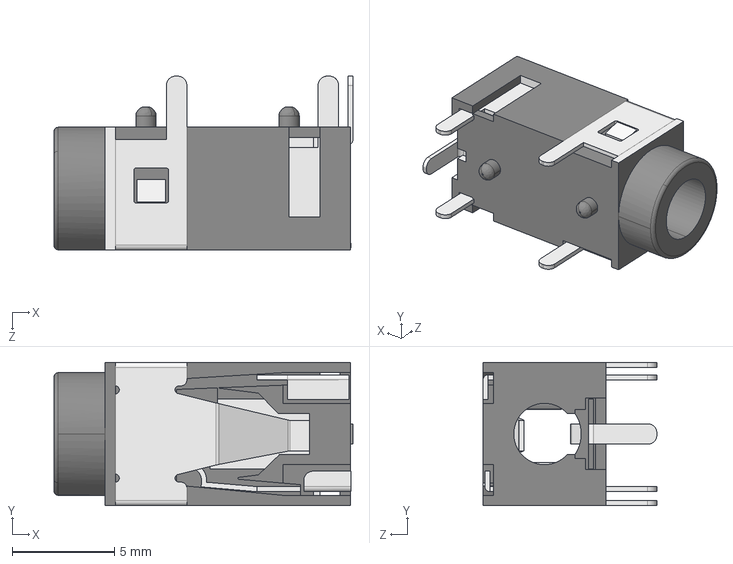
[picture p95: CAD file, 2026-09-27]
STP/PJ-322.step
14.6 x 7.00 x 8.50 mm
