liveboxandy/ZX-Spectrum-48K-Issue-2/STP/STC_4116.step

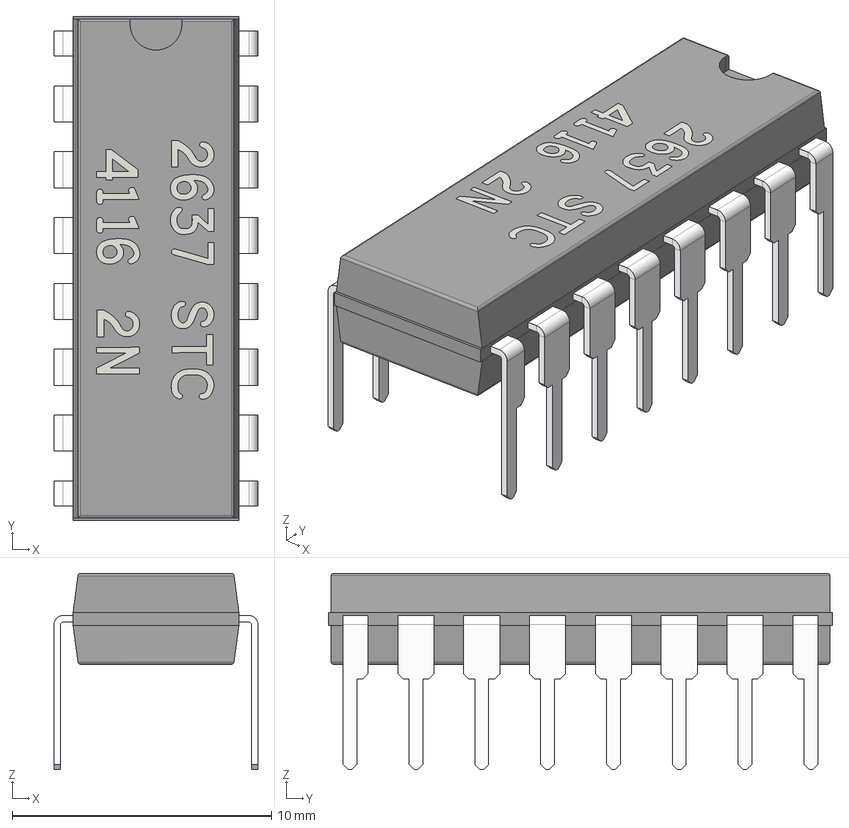
[picture p97: CAD file, 2026-09-27]
STP/STC_4116.step
7.87 x 19.5 x 7.57 mm
Basic - DIP 7.62 v3
DIP Pin 14-20 v3
DIP Pin 14-20 v3(Mirror)
