liveboxandy/ZX-Spectrum-48K-Issue-2/STP/LM78xx_inc_Heatsink v6.step

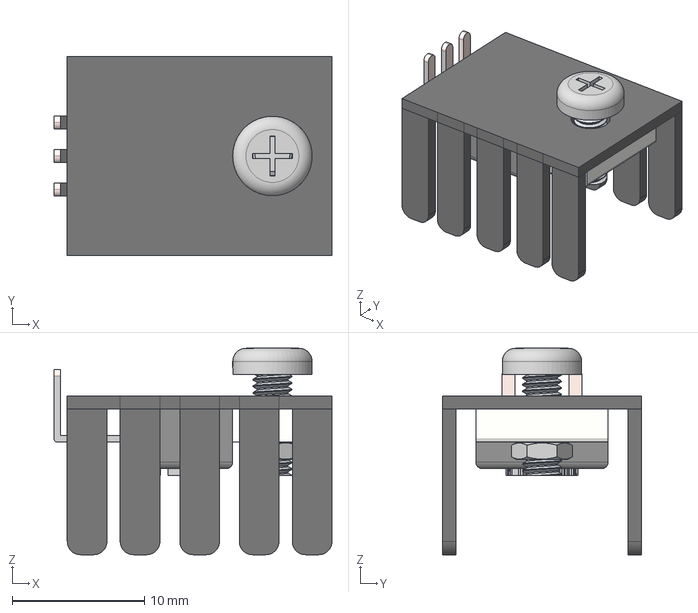
[picture p98: CAD file, 2026-09-27]
STP/LM78xx_inc_Heatsink v6.step
21.0 x 15.0 x 15.6 mm
