liveboxandy/ZX-Spectrum-48K-Issue-2/STP/TO-92S_Normal_LF42_rev1.0.STEP

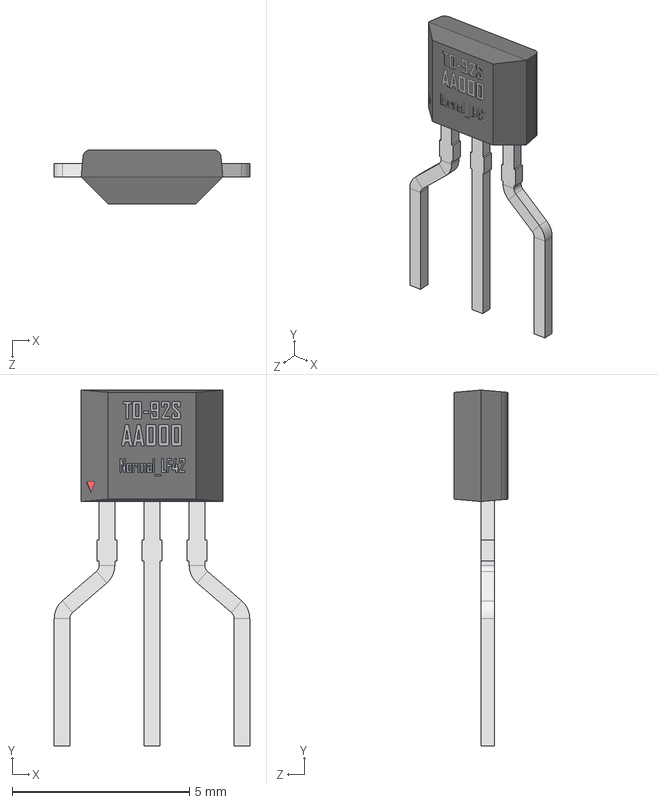
[picture p99: CAD file, 2026-09-27]
STP/TO-92S_Normal_LF42_rev1.0.STEP
5.52 x 10.1 x 1.52 mm
