liveboxandy/ZX-Spectrum-48K-Issue-2/STP/ROM HITACHI HN613128P.step

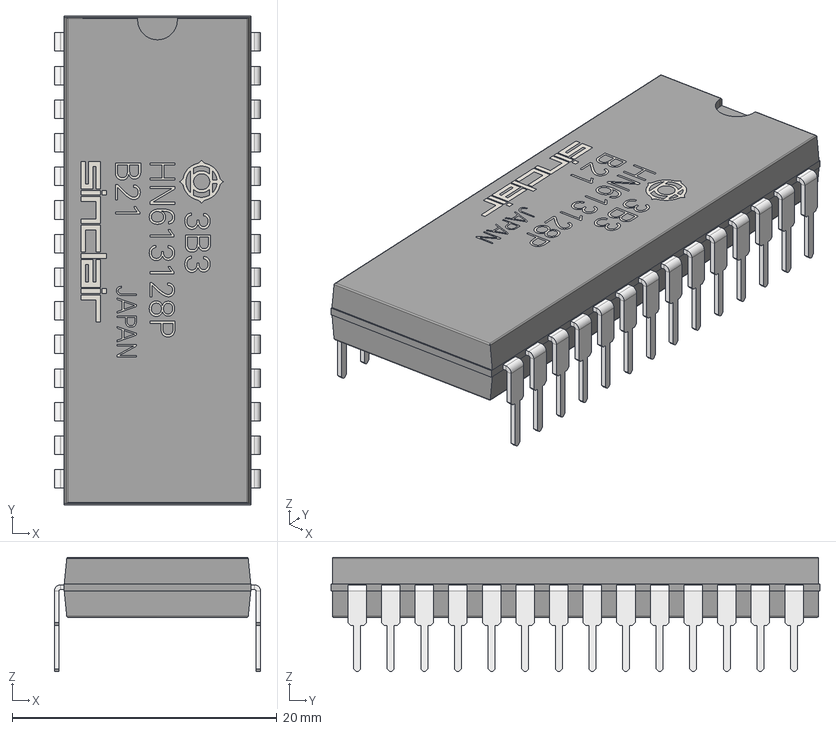
[picture p102: CAD file, 2026-09-27]
STP/ROM HITACHI HN613128P.step
15.6 x 37.0 x 8.64 mm
Basic - DIP40 Wide v2
DIP Pin v2
DIP Pin v2(Mirror)
