liveboxandy/ZX-Spectrum-48K-Issue-2/STP/Z80 - SGS.step

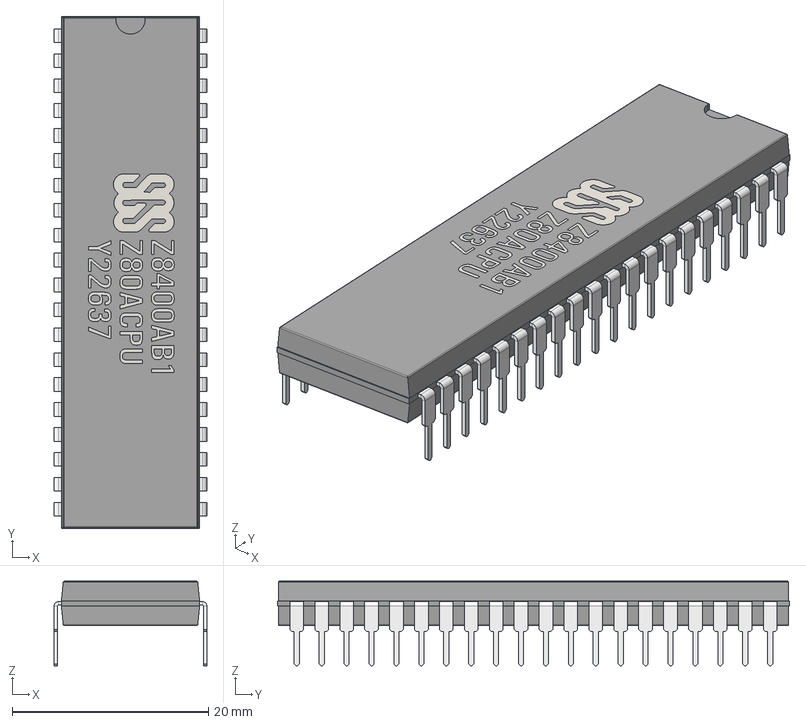
[picture p103: CAD file, 2026-09-27]
STP/Z80 - SGS.step
15.6 x 52.2 x 8.64 mm
Basic - DIP40 Wide v2
DIP Pin v2
DIP Pin v2(Mirror)
