liveboxandy/ZX-Spectrum-48K-Issue-2/STP/RF MOD Astec UM1233 E36.step

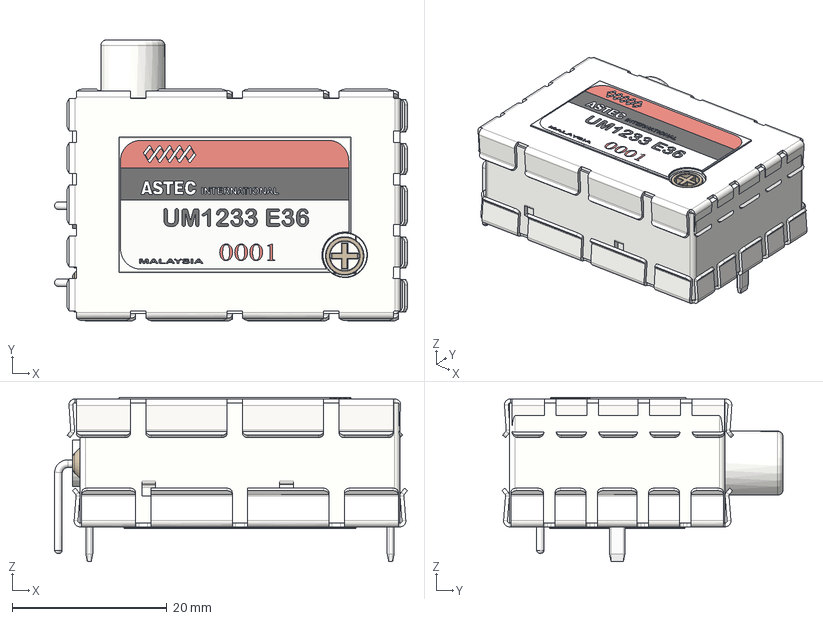
[picture p104: CAD file, 2026-09-27]
STP/RF MOD Astec UM1233 E36.step
45.7 x 36.4 x 21.3 mm
Metal Body
Lid Bottom
Lid Top
